Sadrita404/Twin-Key/Images/48.png

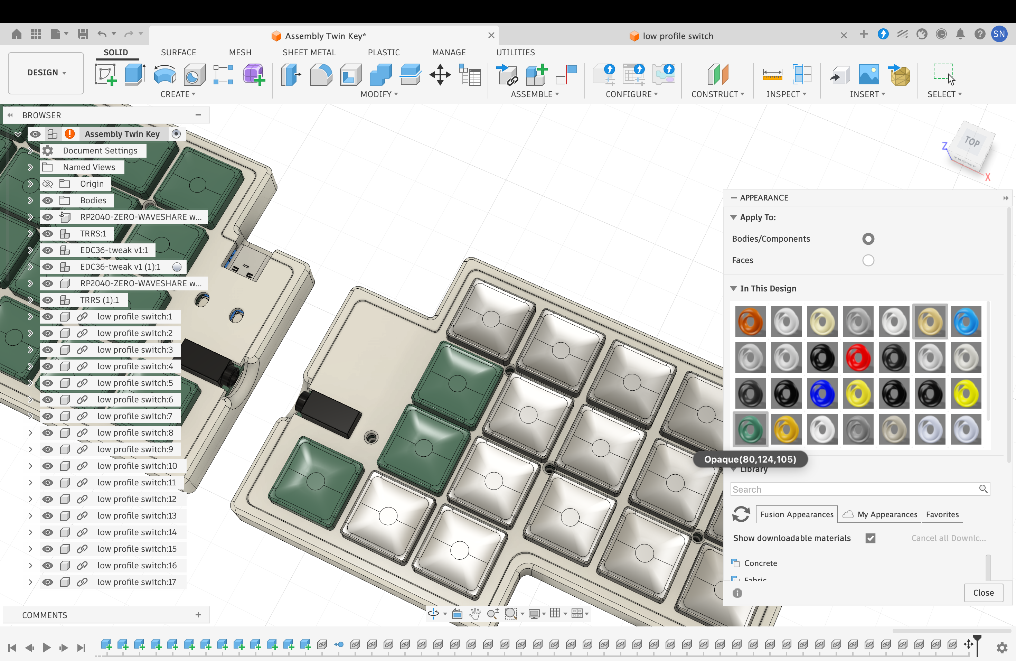
Images/48.png
