Sadrita404/Twin-Key/Bill/bill 1.png

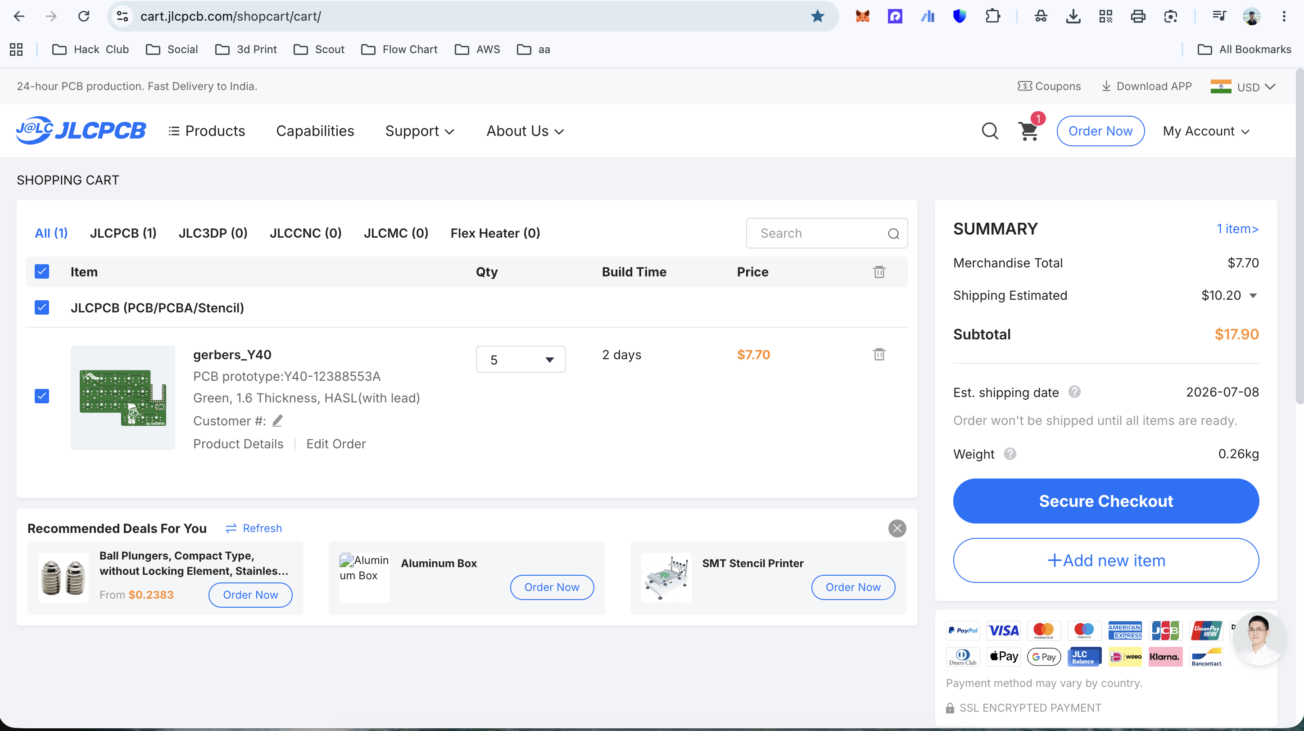
Bill/bill 1.png
