Sadrita404/Twin-Key/Bill/bill 2.png

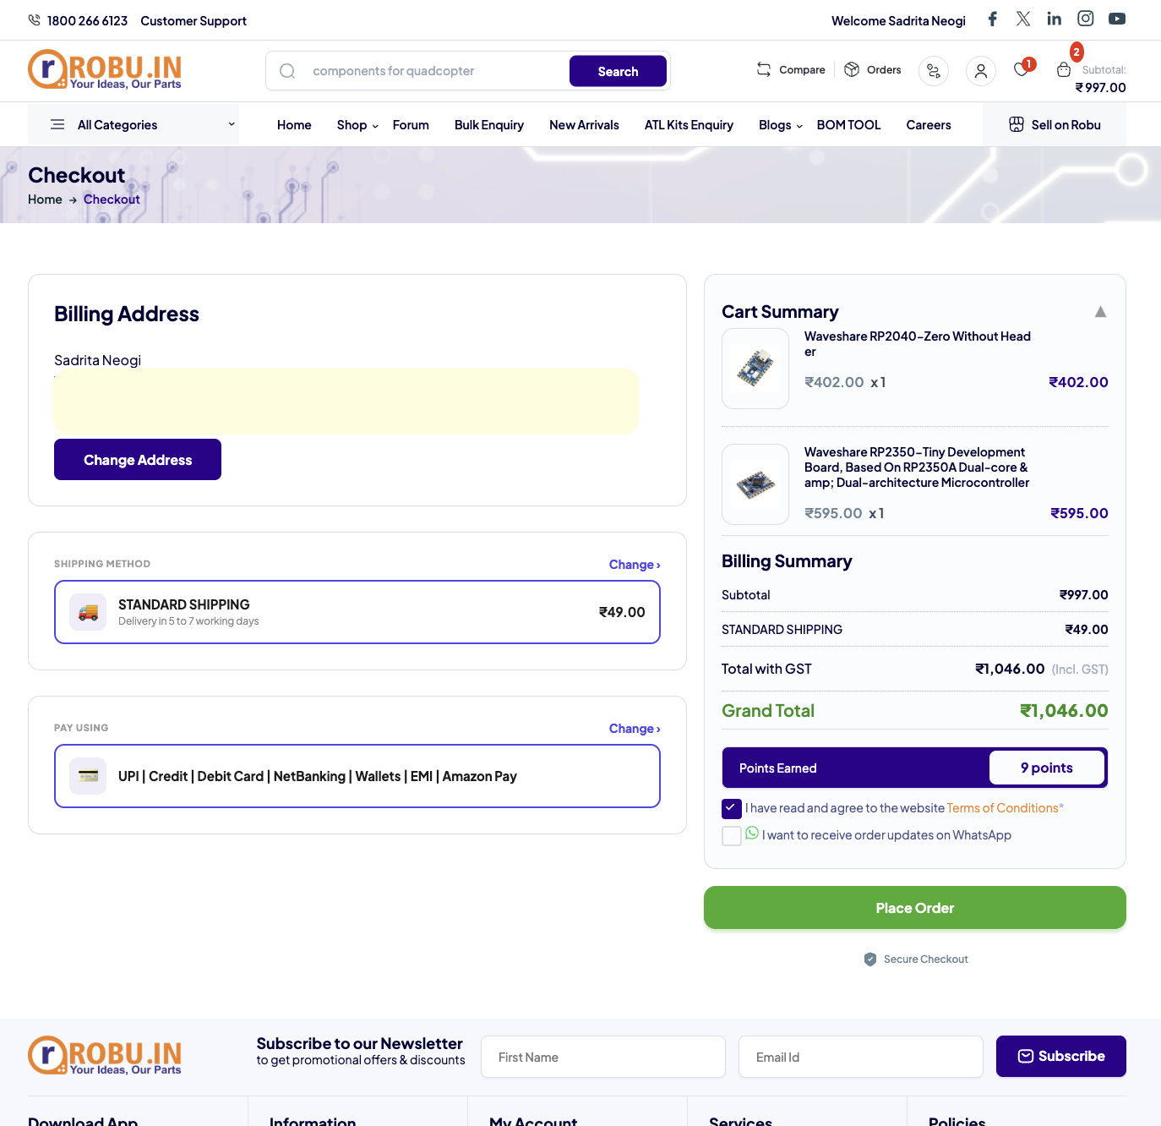
Bill/bill 2.png
