Sadrita404/Twin-Key/Bill/bill 3.png

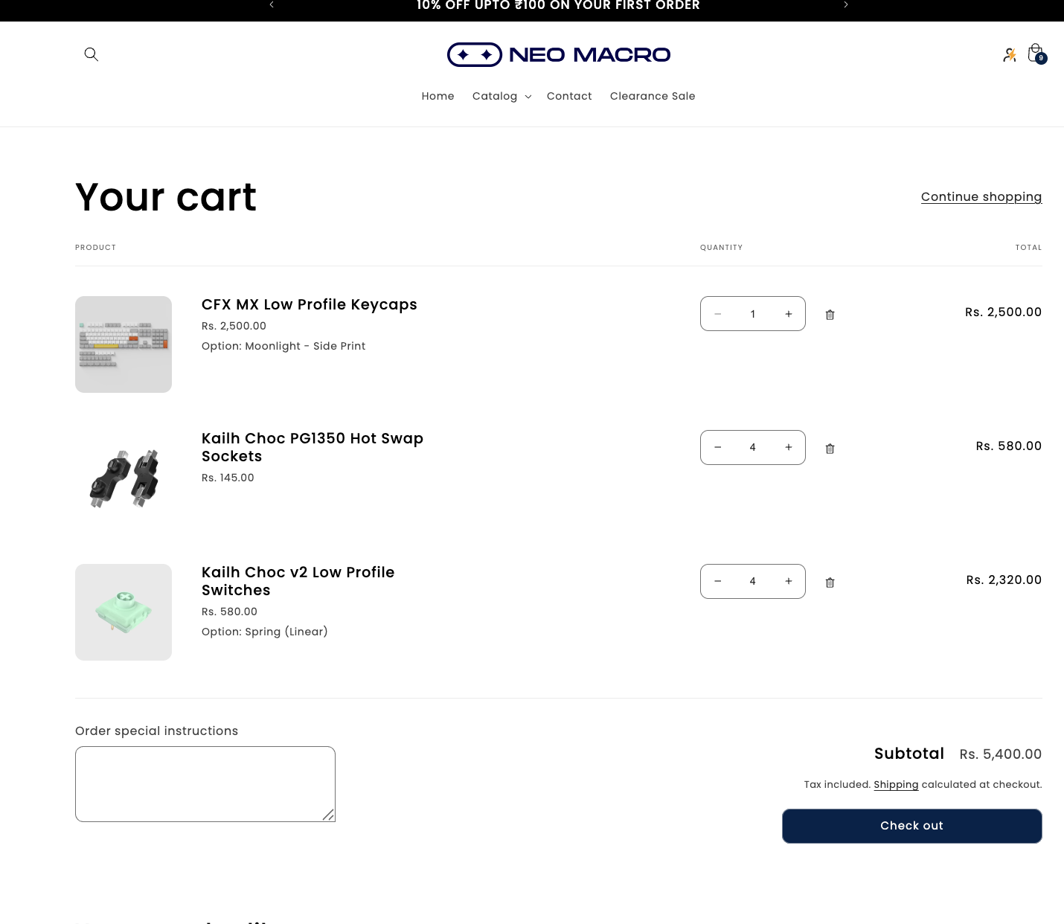
Bill/bill 3.png
