Sadrita404/Twin-Key/Bill/bill 4.png

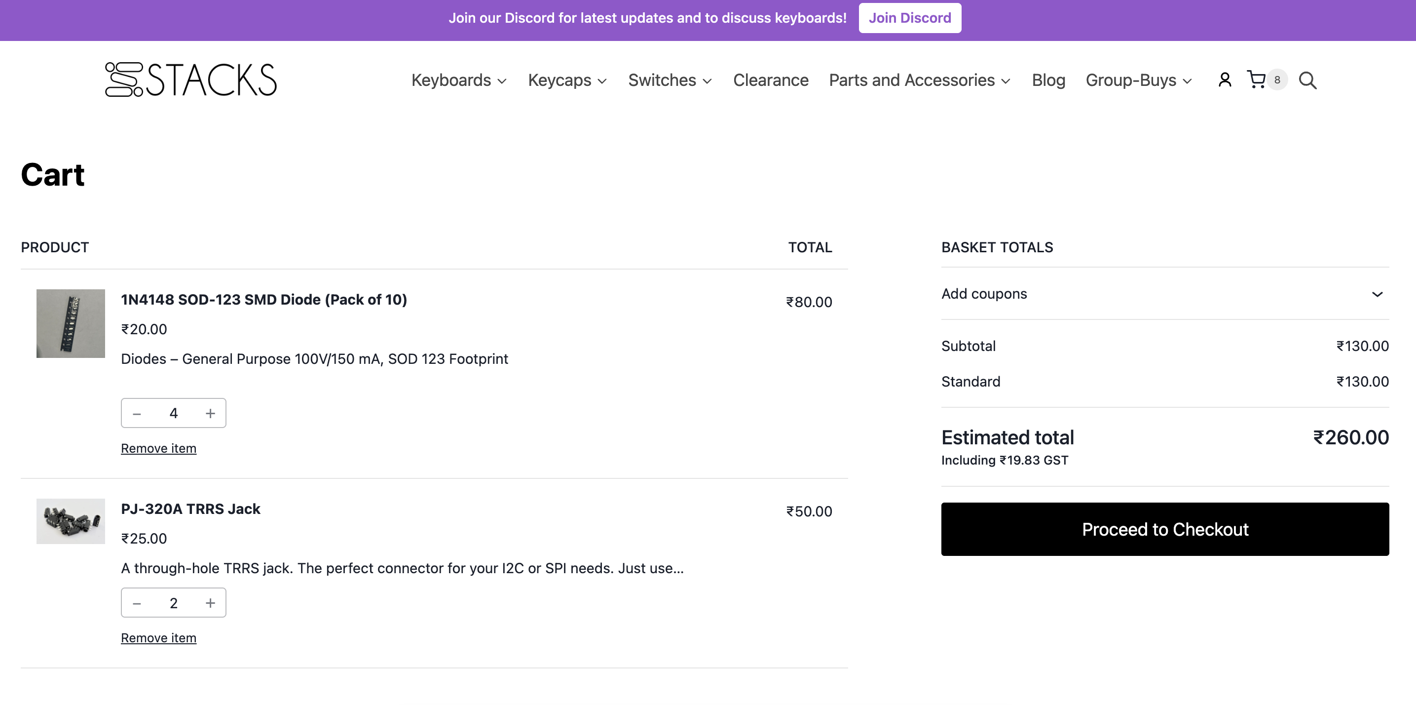
Bill/bill 4.png
