Sadrita404/Twin-Key/Bill/bill 5.png

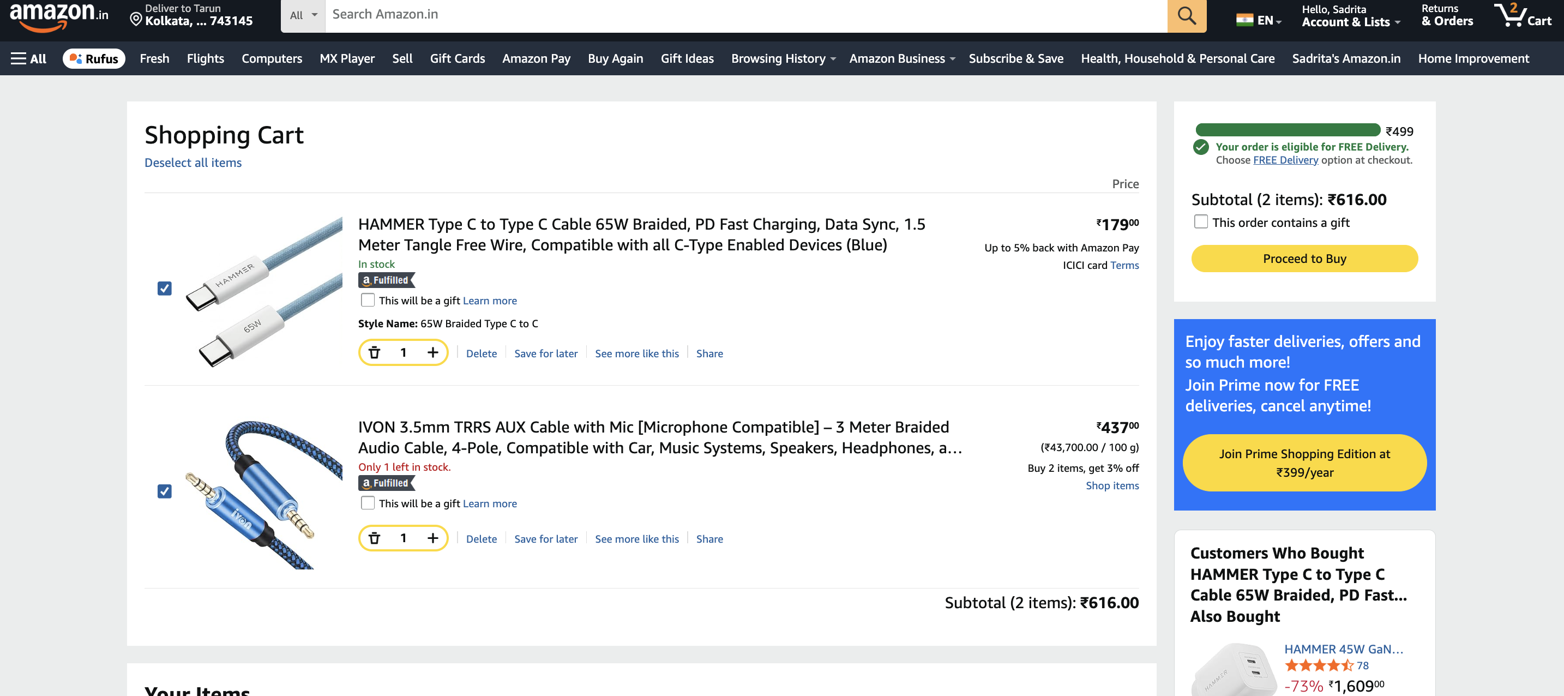
Bill/bill 5.png
