Sadrita404/Twin-Key/Images/1.png

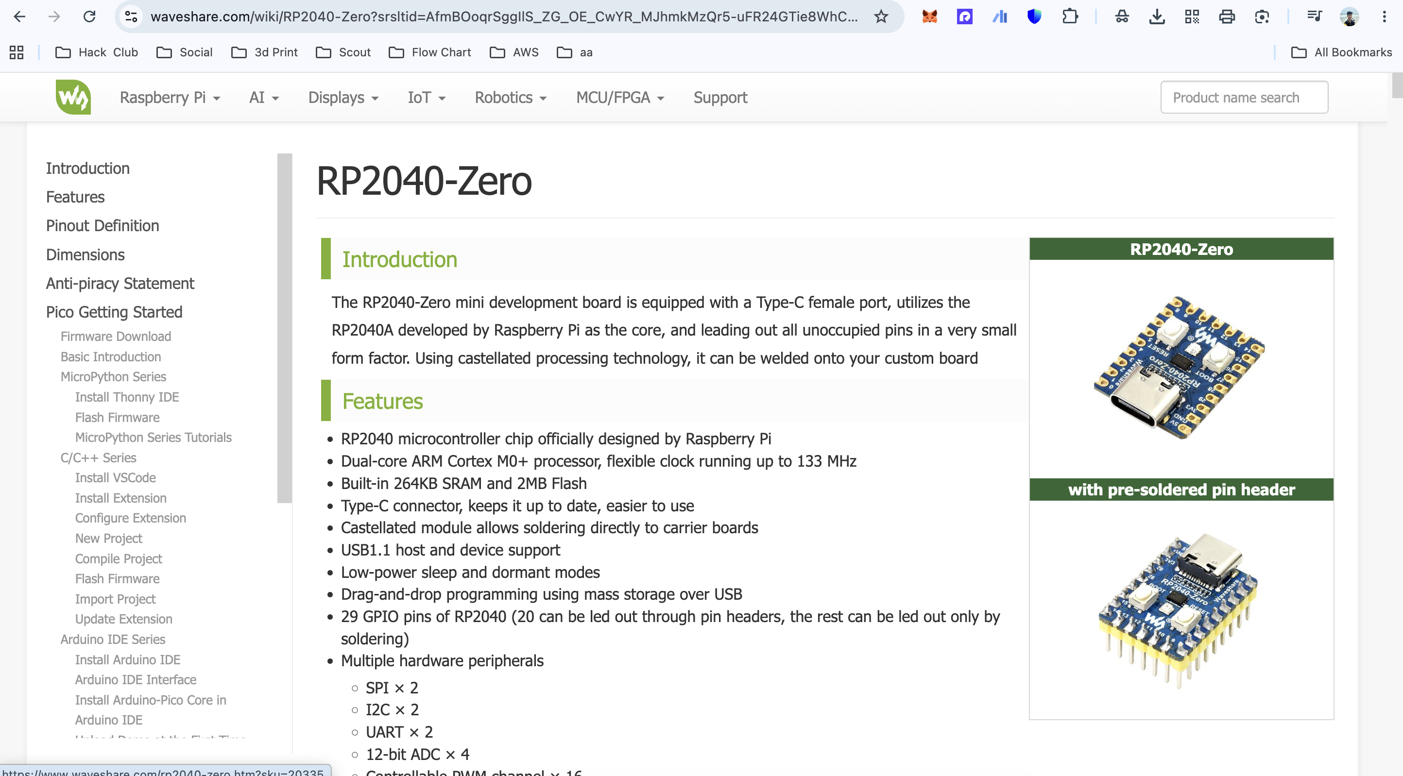
Images/1.png
