Sadrita404/Twin-Key/Images/2.png

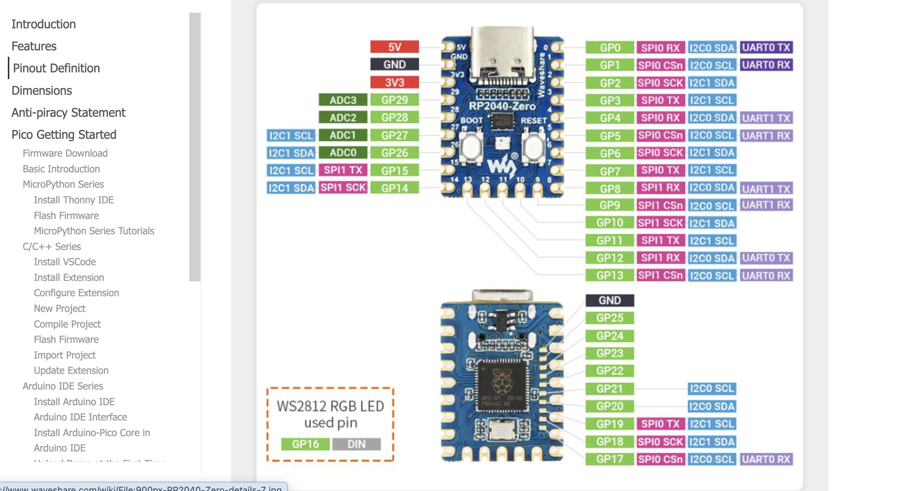
Images/2.png
