Sadrita404/Twin-Key/Images/3.png

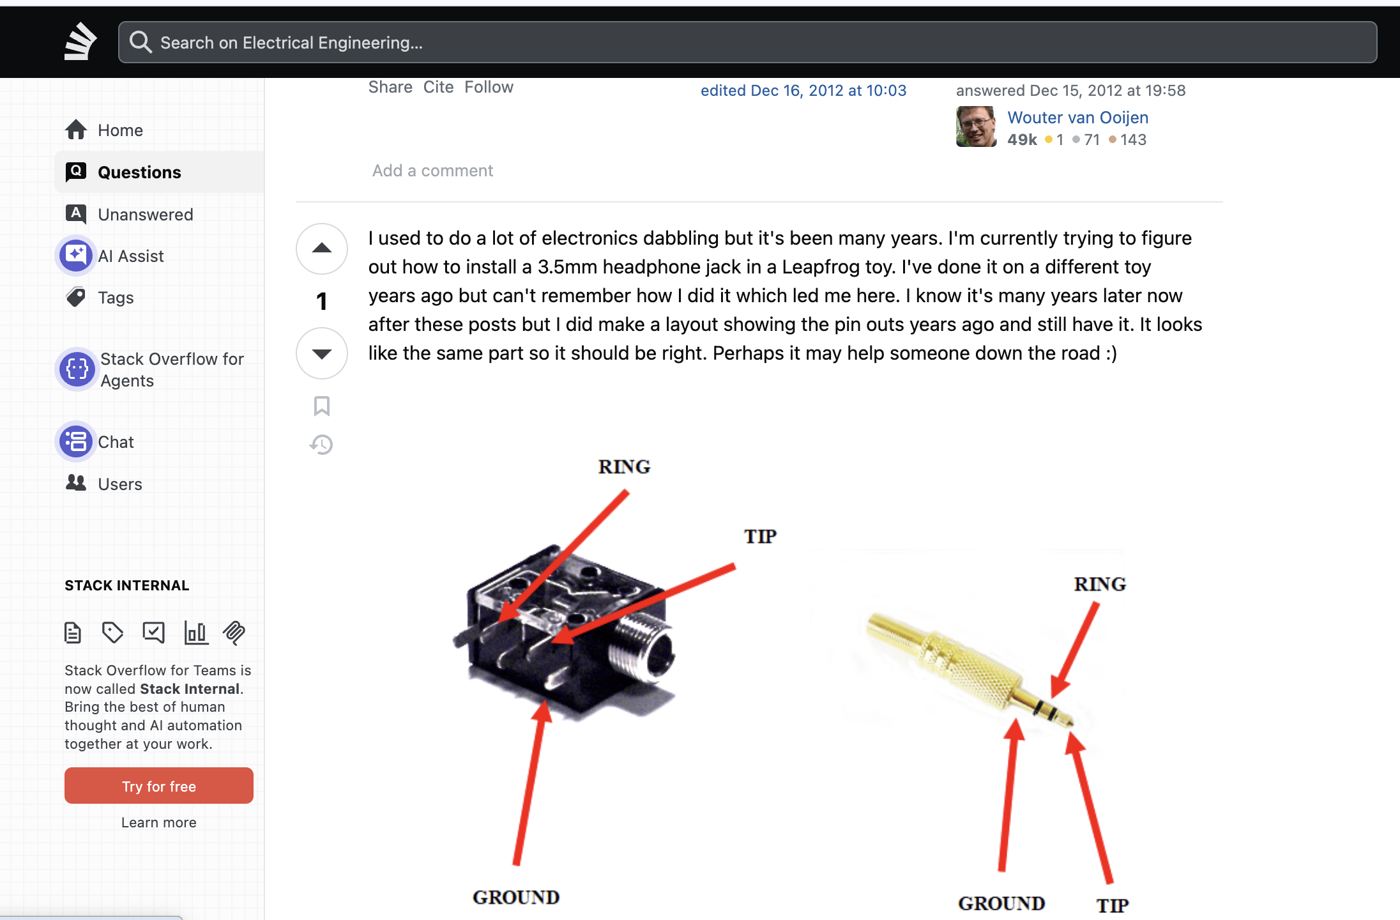
Images/3.png
