Sadrita404/Twin-Key/Images/4.png

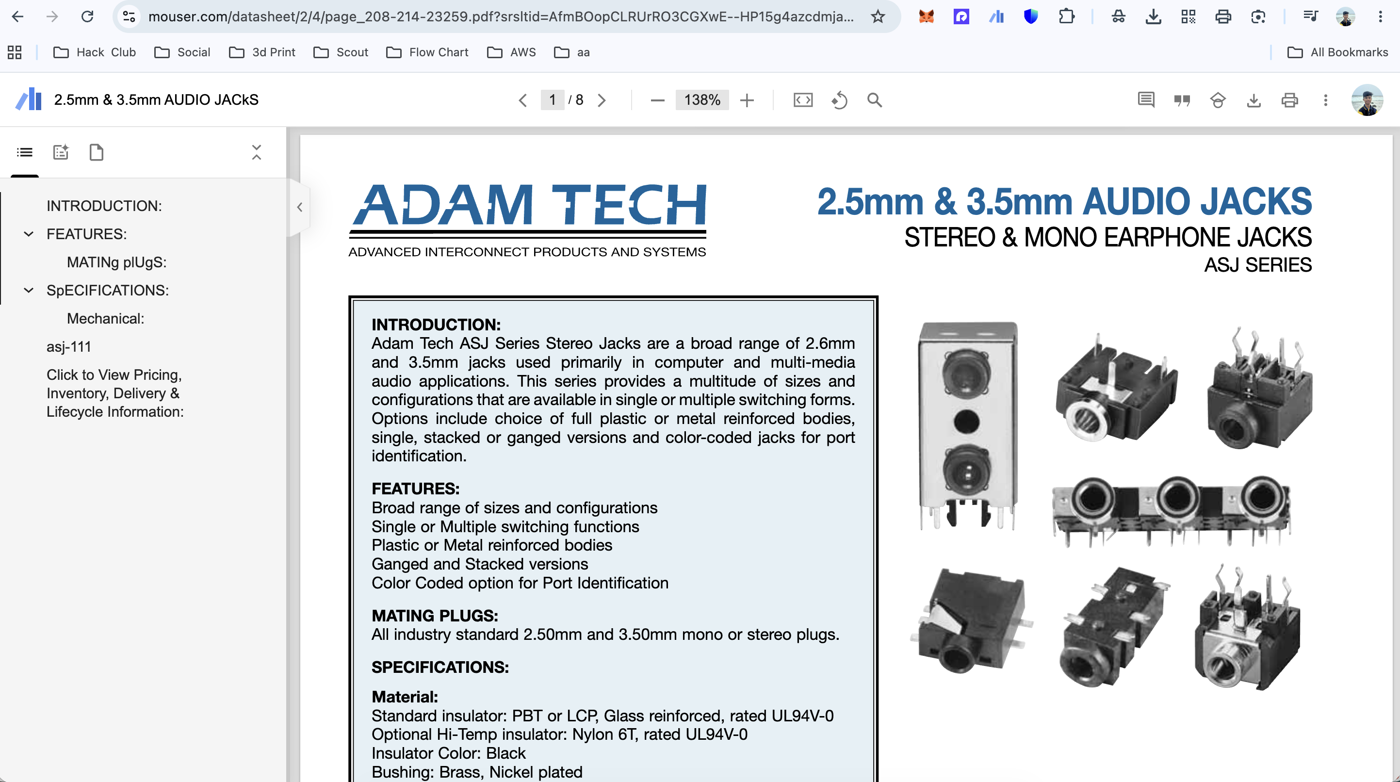
Images/4.png
