Sadrita404/Twin-Key/Images/5.png

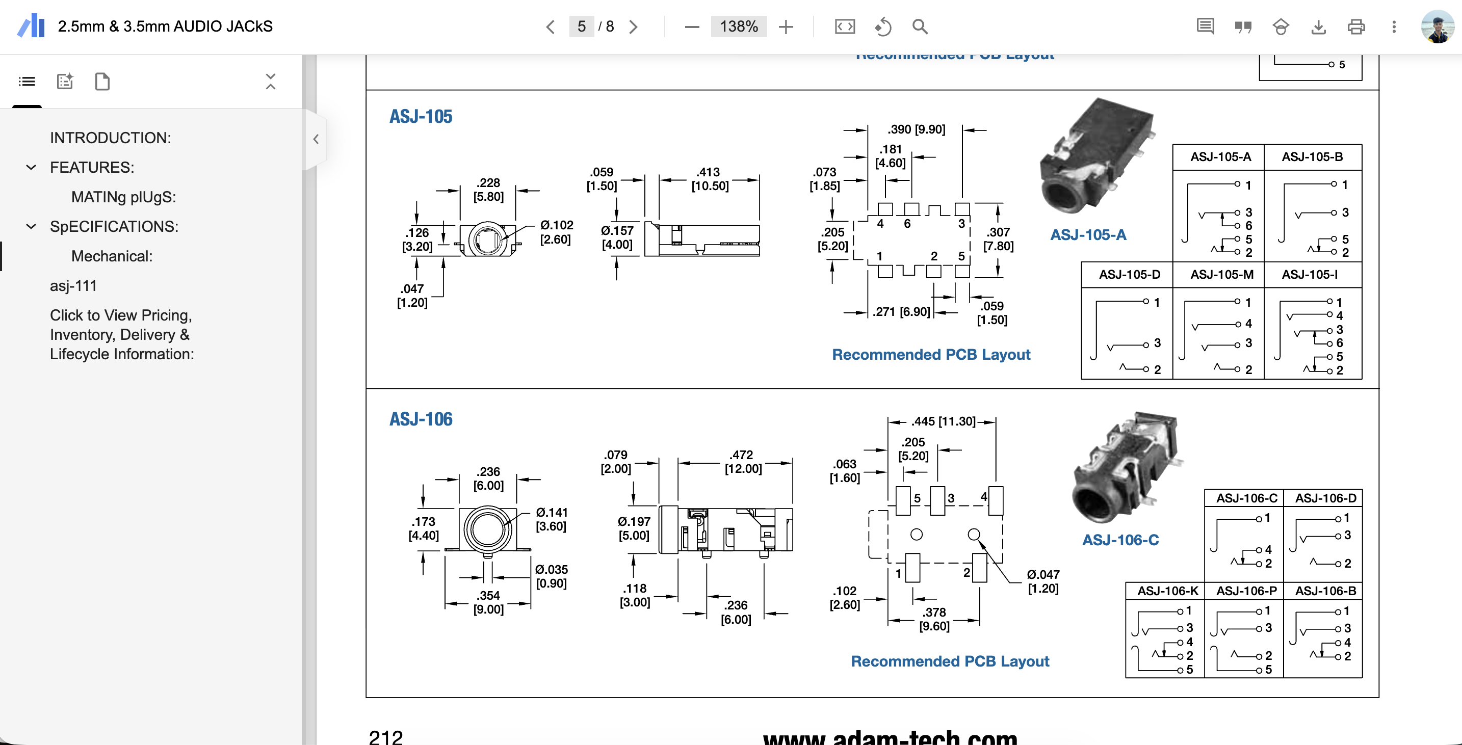
Images/5.png
