Sadrita404/Twin-Key/Images/6.png

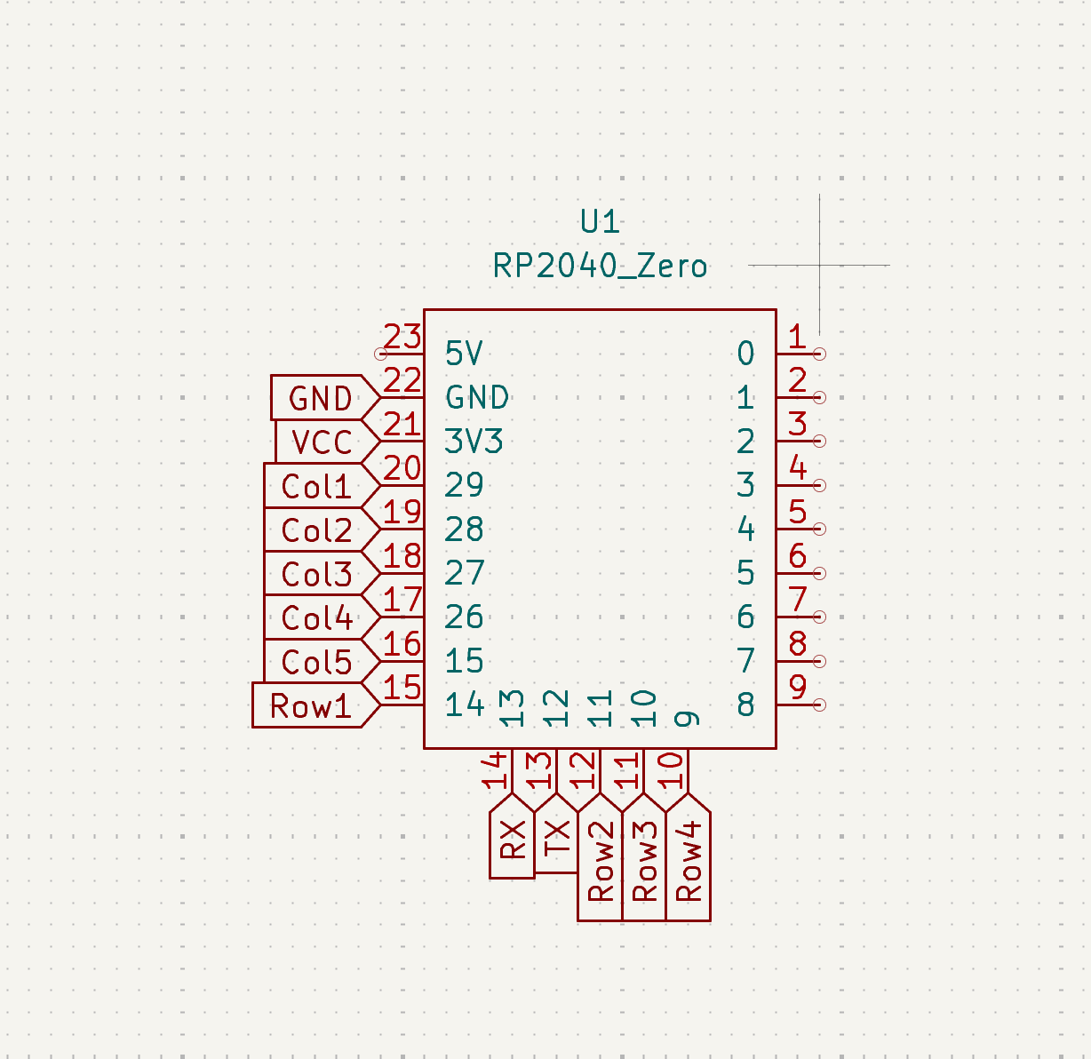
Images/6.png
