Sadrita404/Twin-Key/Images/7.png

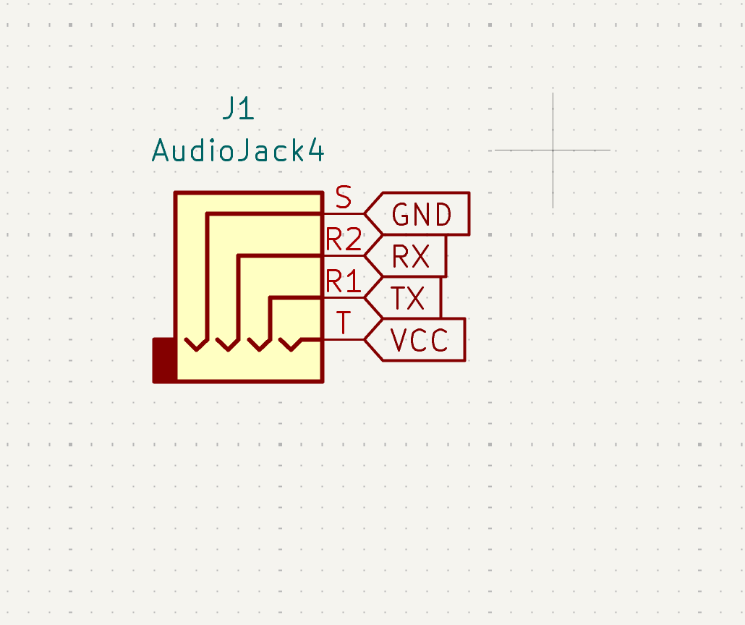
Images/7.png
