Sadrita404/Twin-Key/Images/8.png

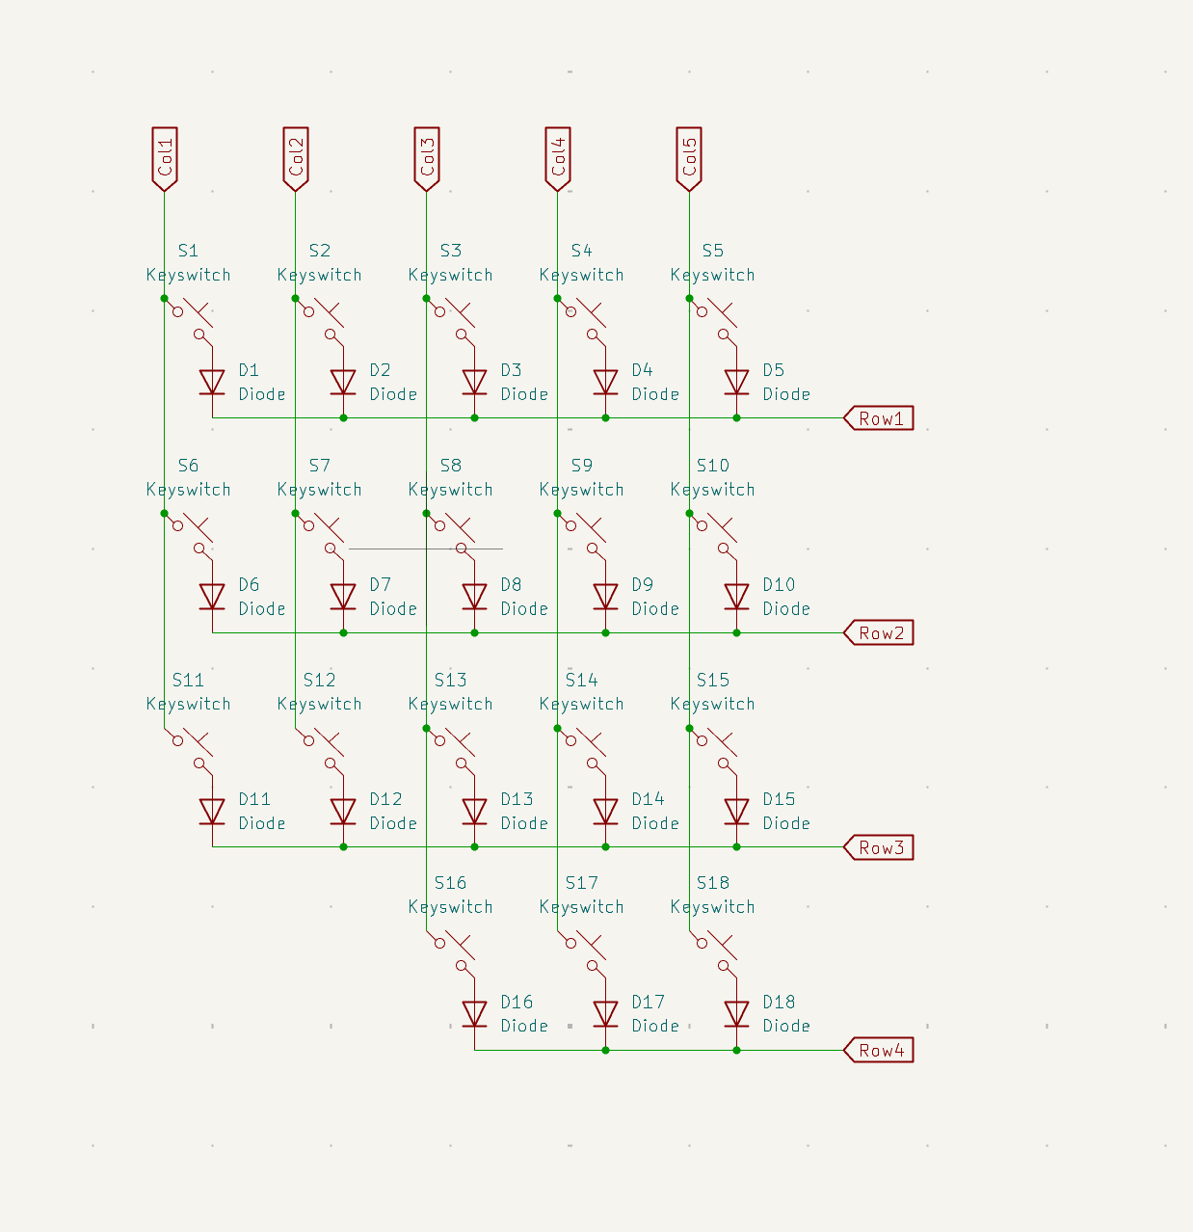
Images/8.png
