Sadrita404/Twin-Key/Images/9.png

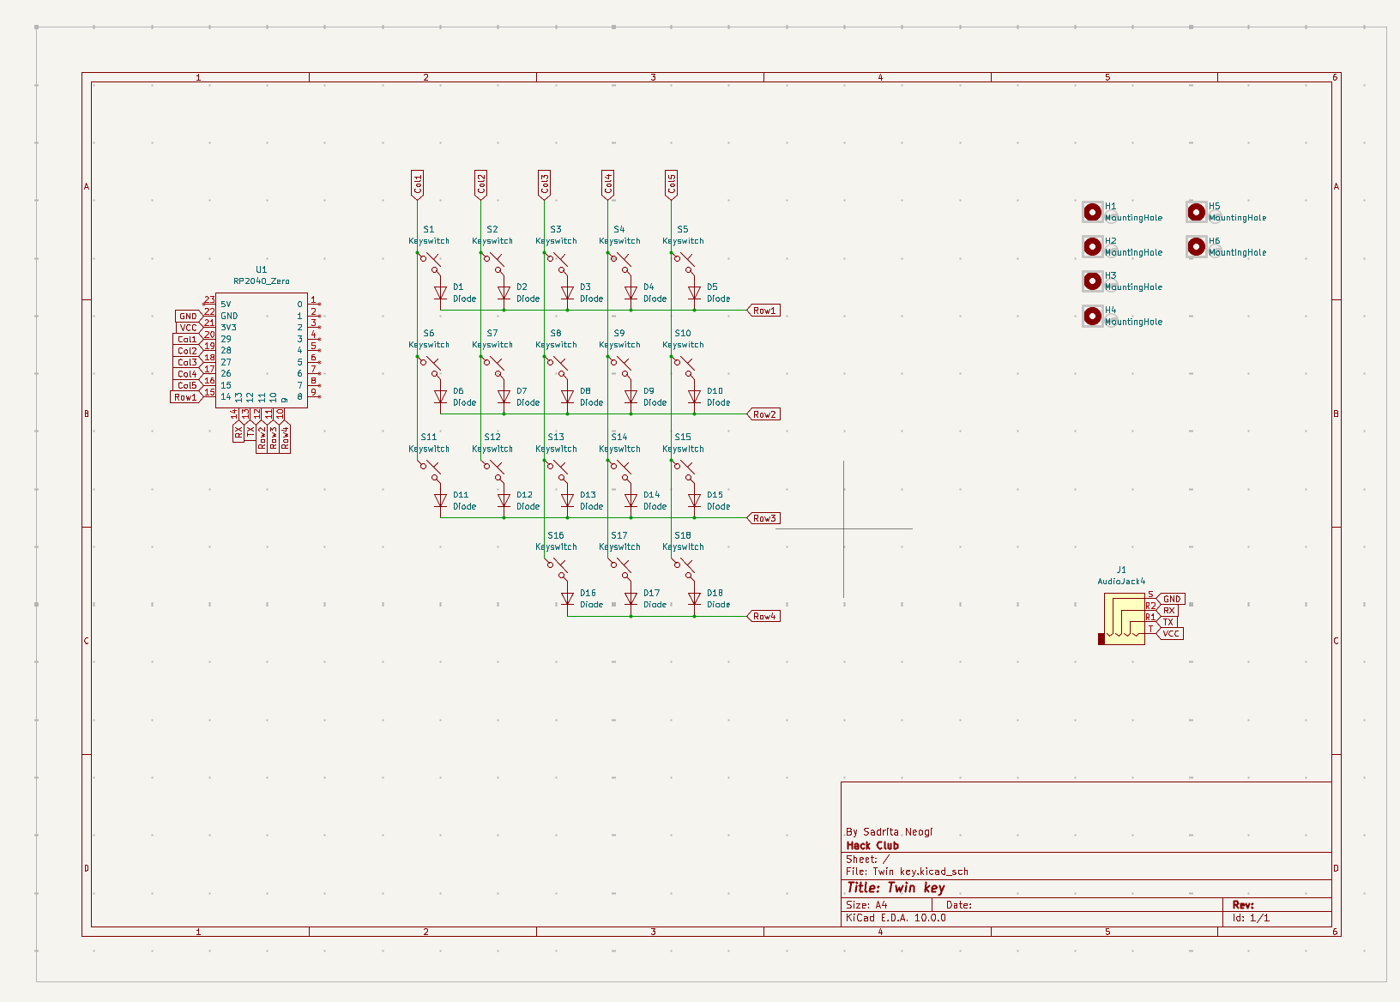
Images/9.png
