Sadrita404/Twin-Key/Images/10.png

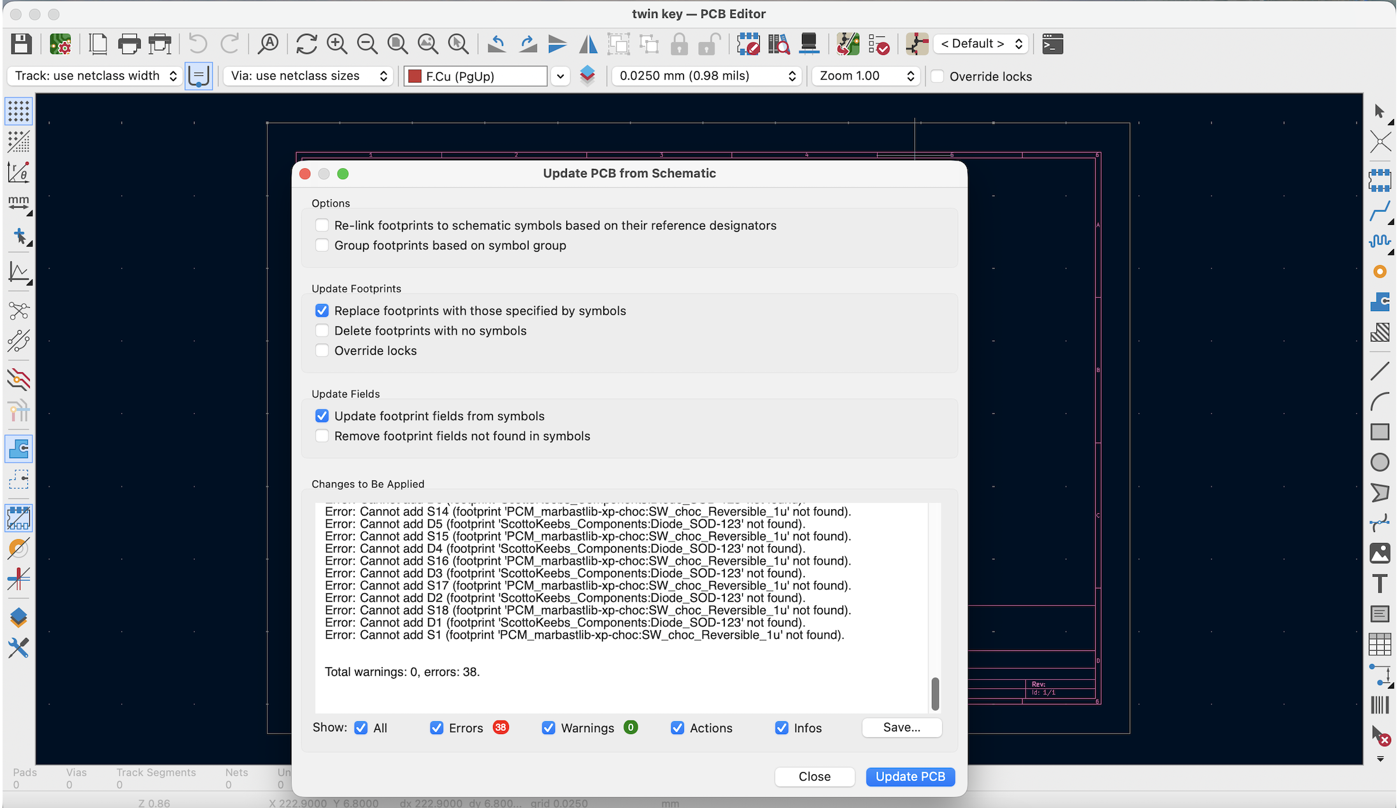
Images/10.png
