Sadrita404/Twin-Key/Images/11.png

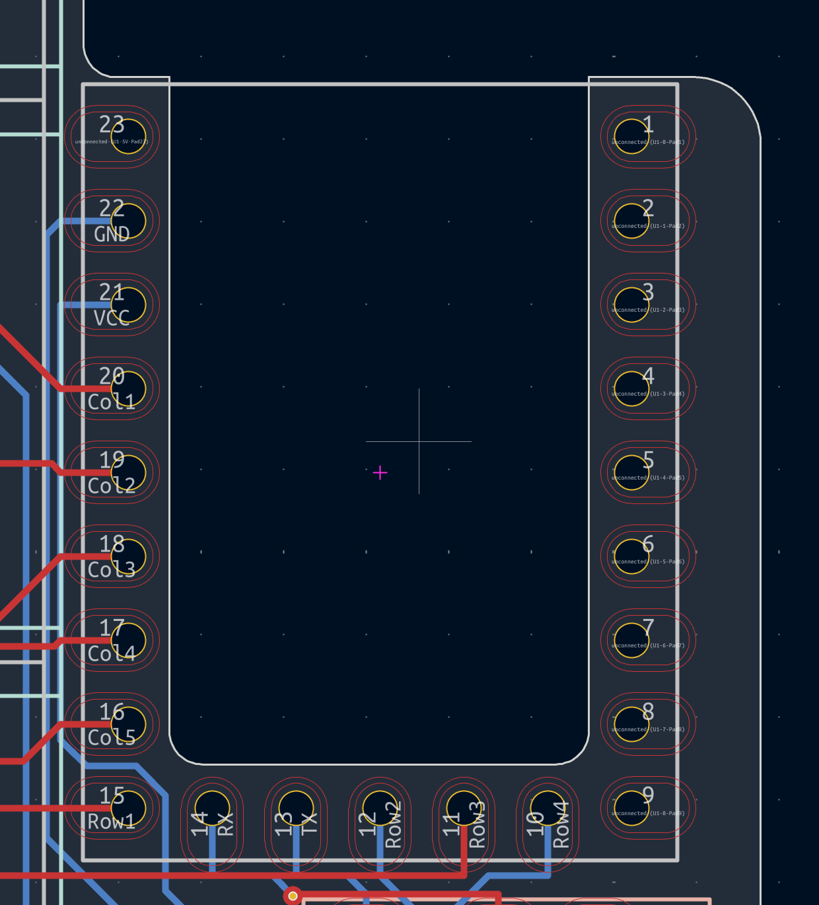
Images/11.png
