Sadrita404/Twin-Key/Images/12.png

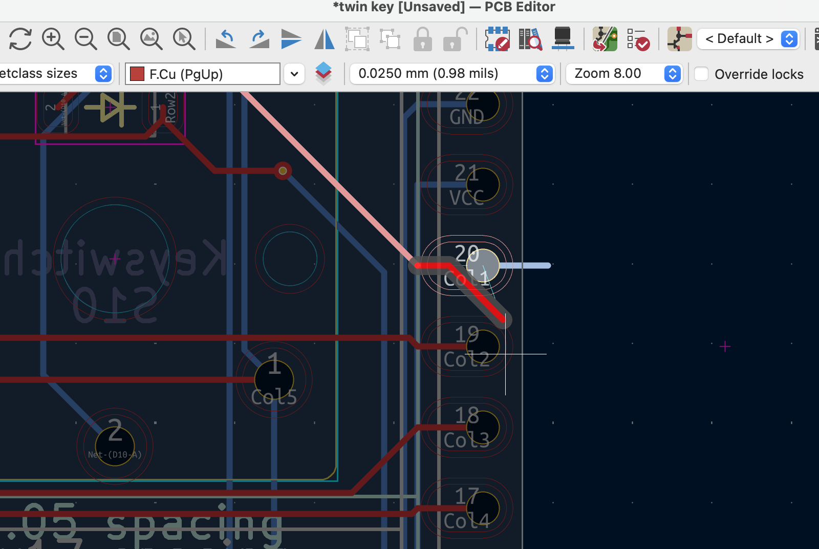
Images/12.png
