Sadrita404/Twin-Key/Images/13.png

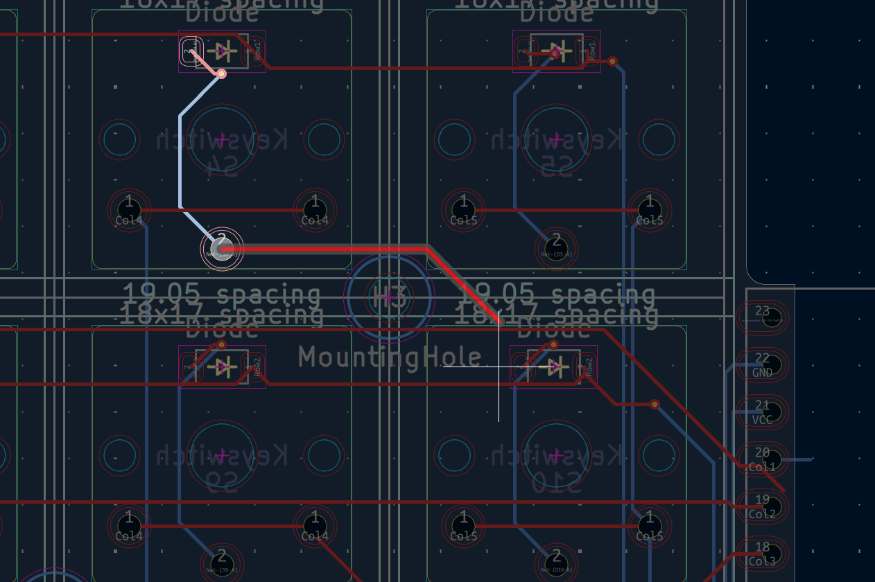
Images/13.png
