Sadrita404/Twin-Key/Images/14.png

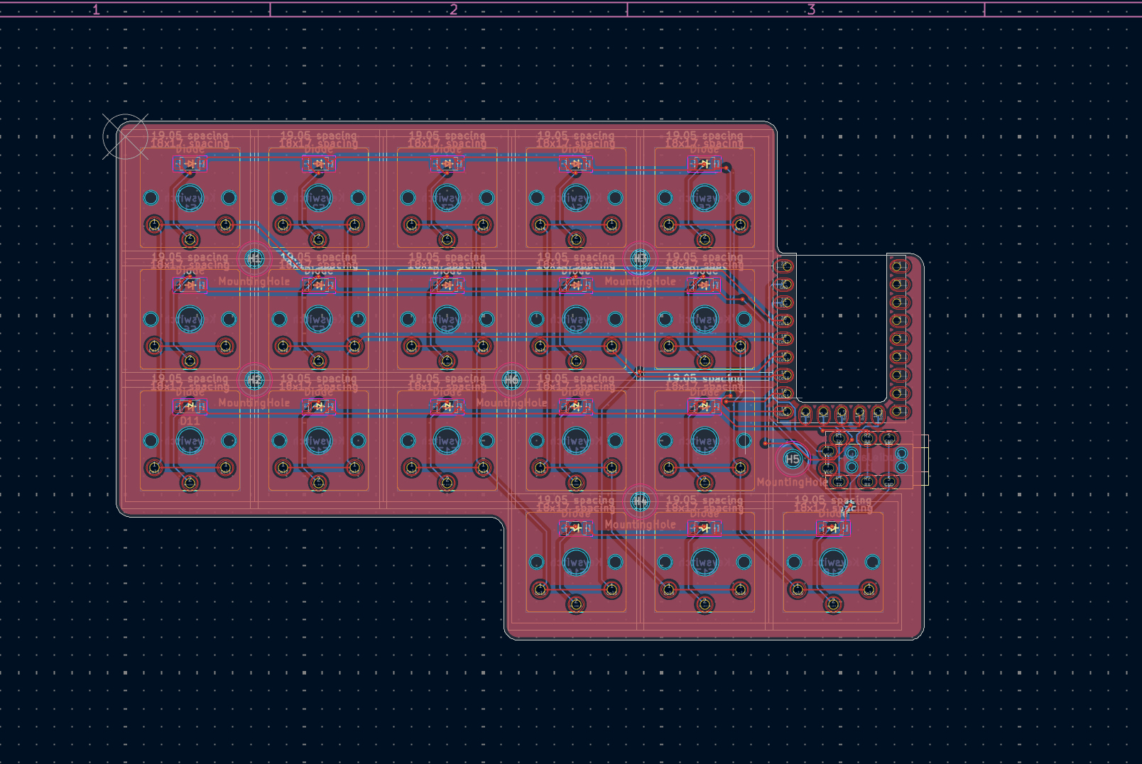
Images/14.png
