Sadrita404/Twin-Key/Images/15.png

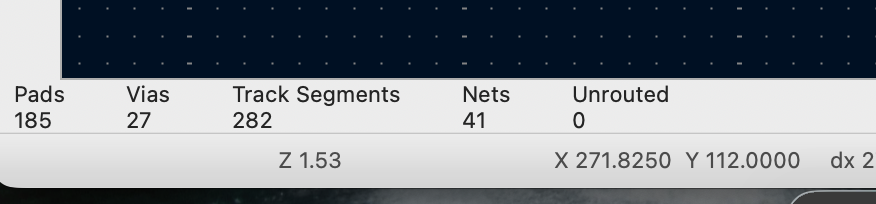
Images/15.png
