Sadrita404/Twin-Key/Images/16.png

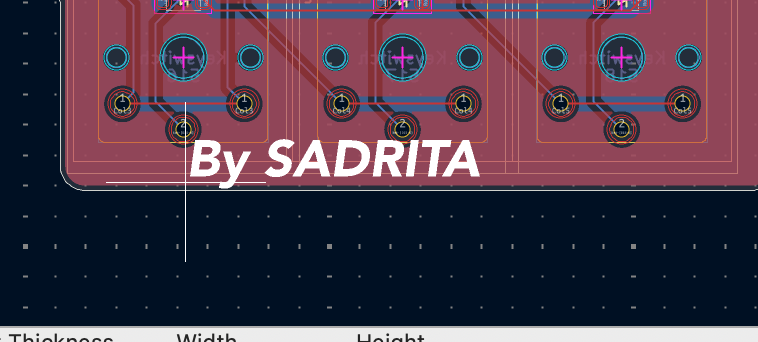
Images/16.png
