Sadrita404/Twin-Key/Images/17.png

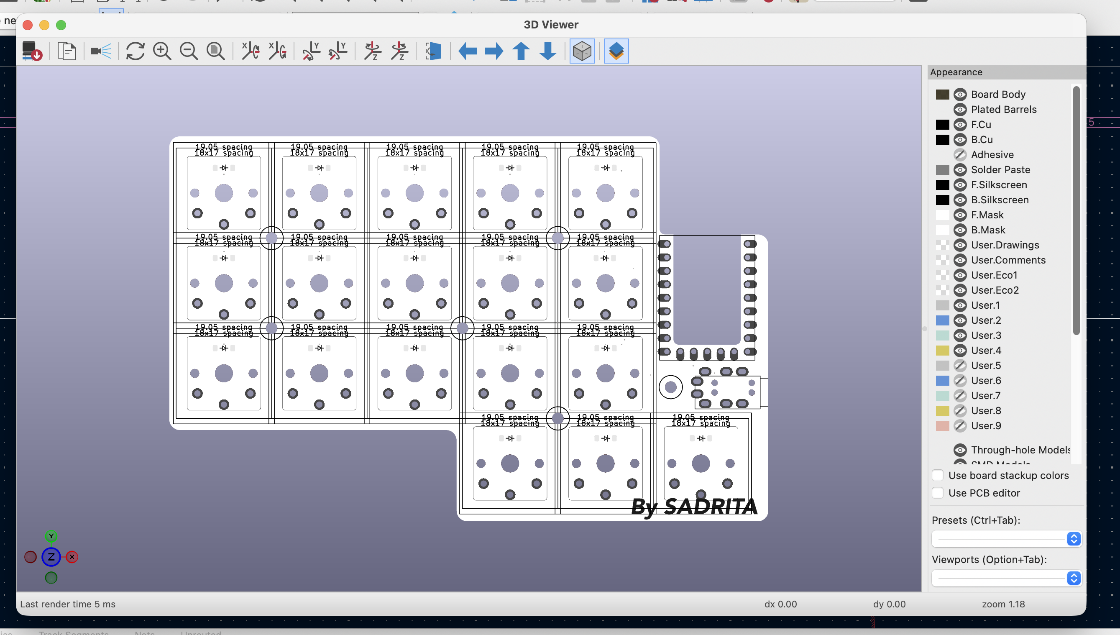
Images/17.png
