Sadrita404/Twin-Key/Images/19.png

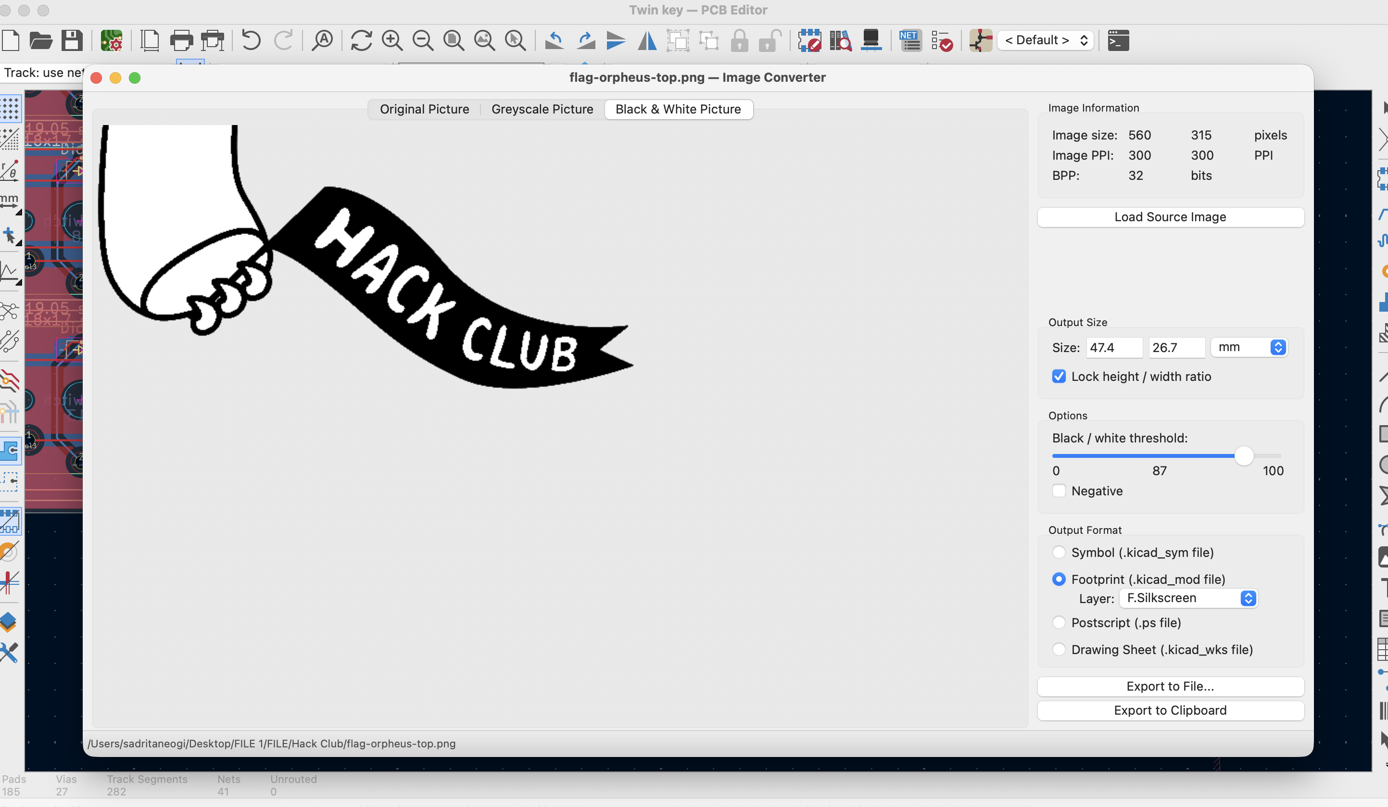
Images/19.png
