Sadrita404/Twin-Key/Images/20.png

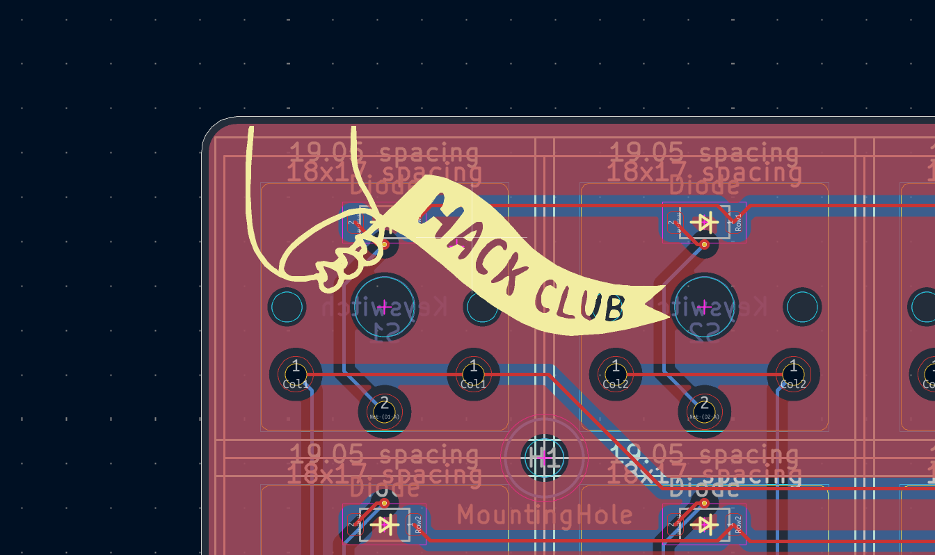
Images/20.png
