Sadrita404/Twin-Key/Images/21.png

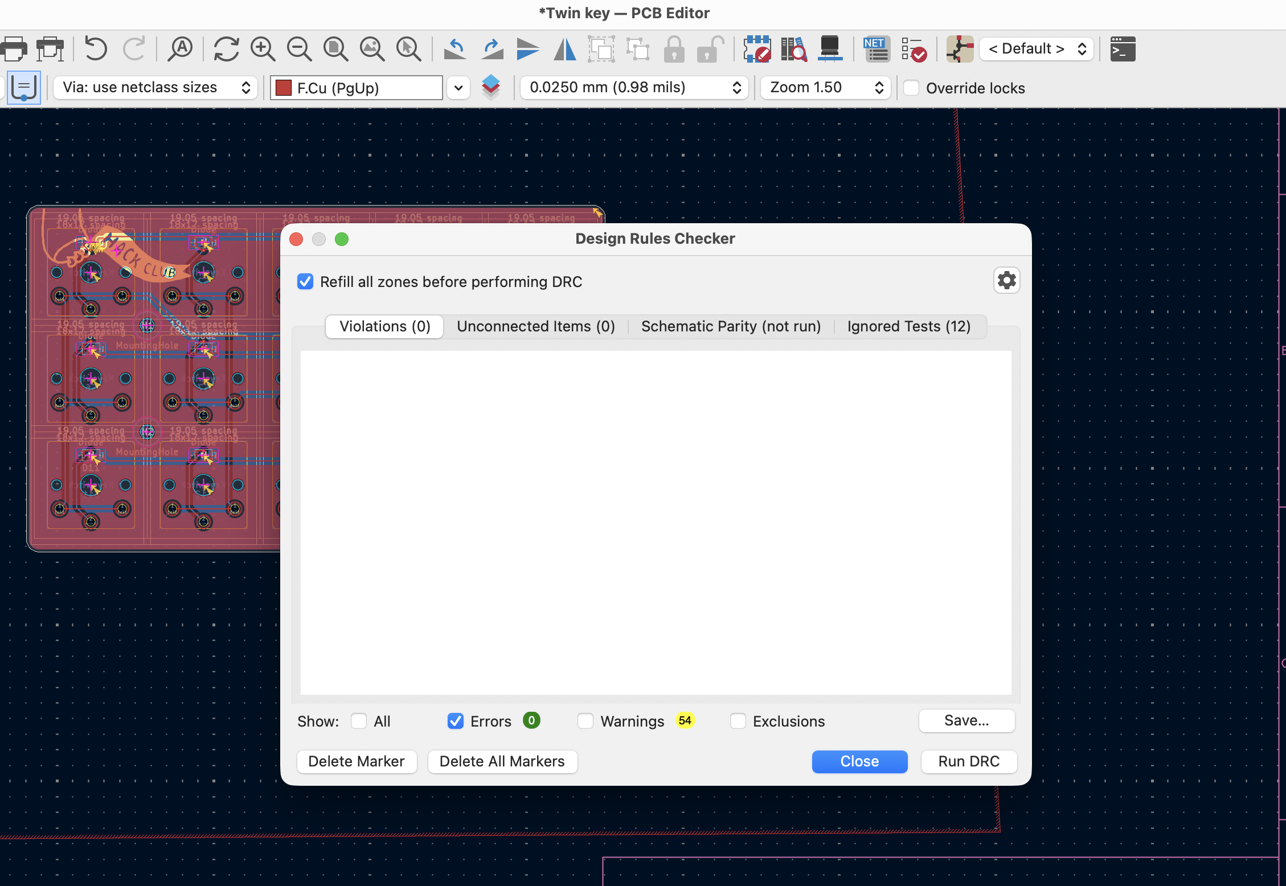
Images/21.png
