Sadrita404/Twin-Key/Images/22.png

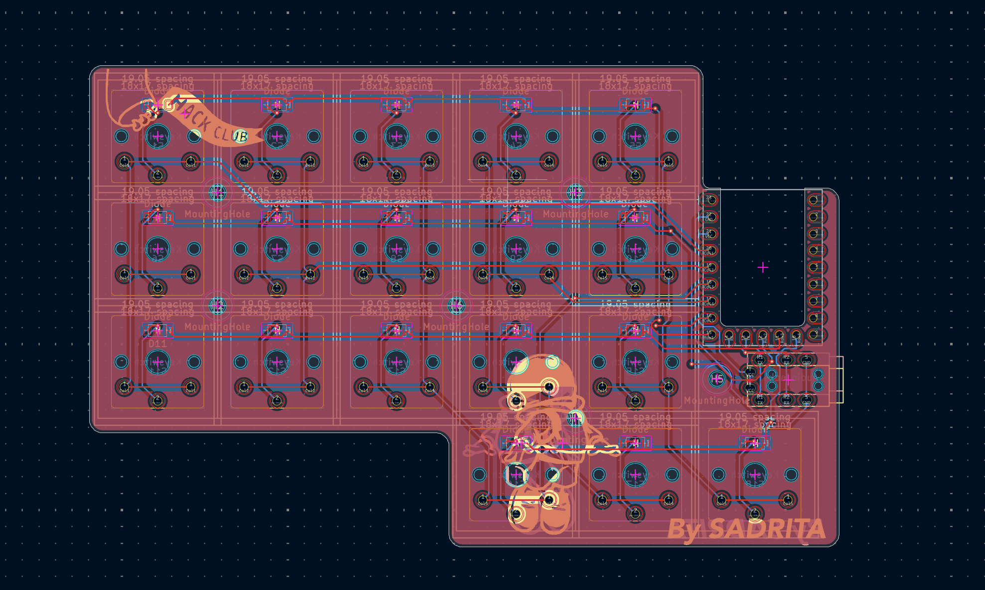
Images/22.png
