Sadrita404/Twin-Key/Images/23.png

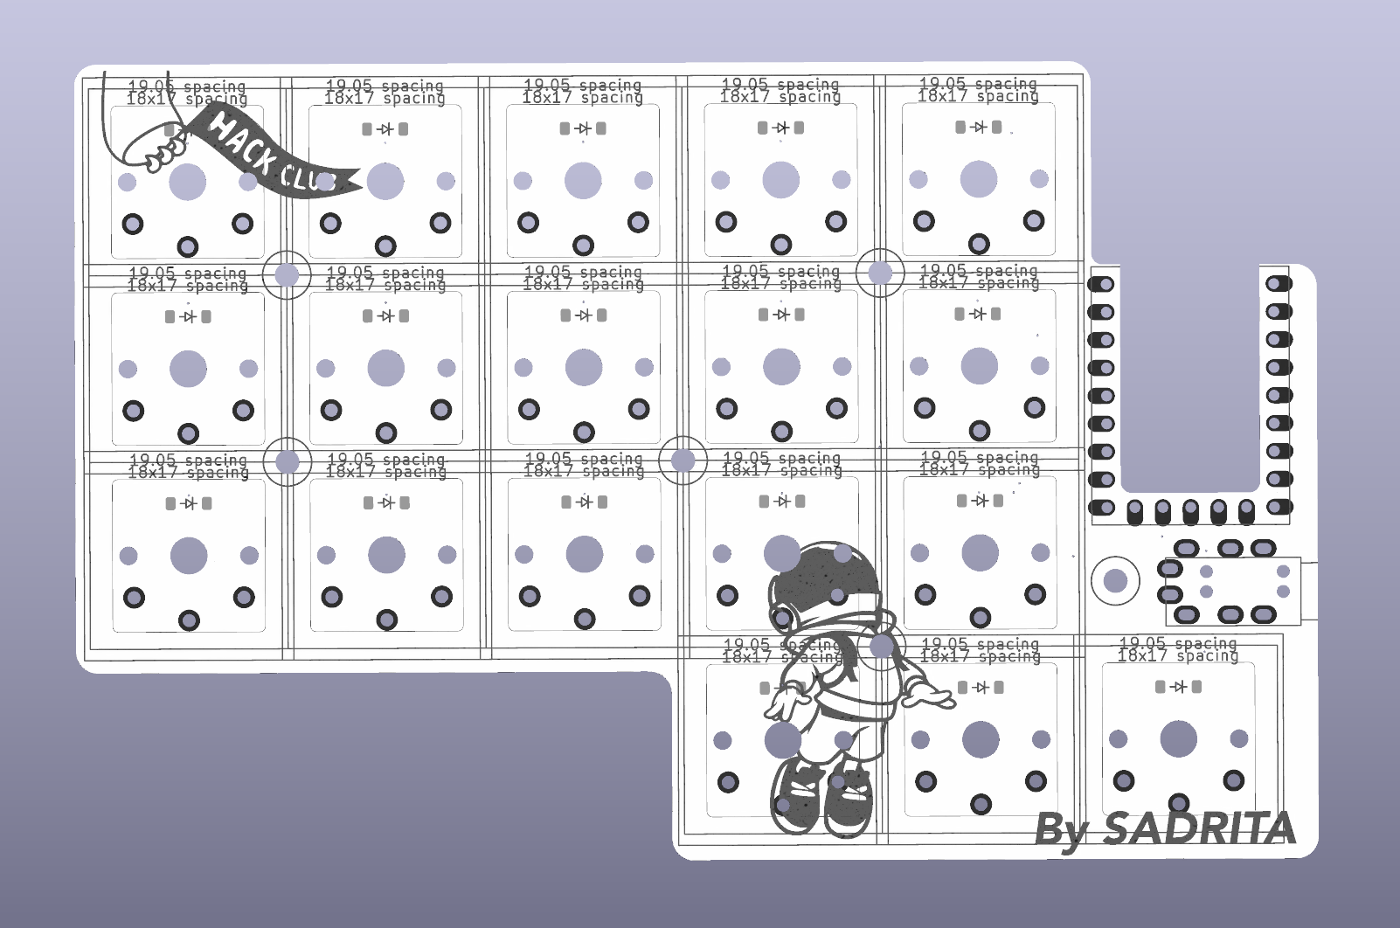
Images/23.png
