Sadrita404/Twin-Key/Images/24.png

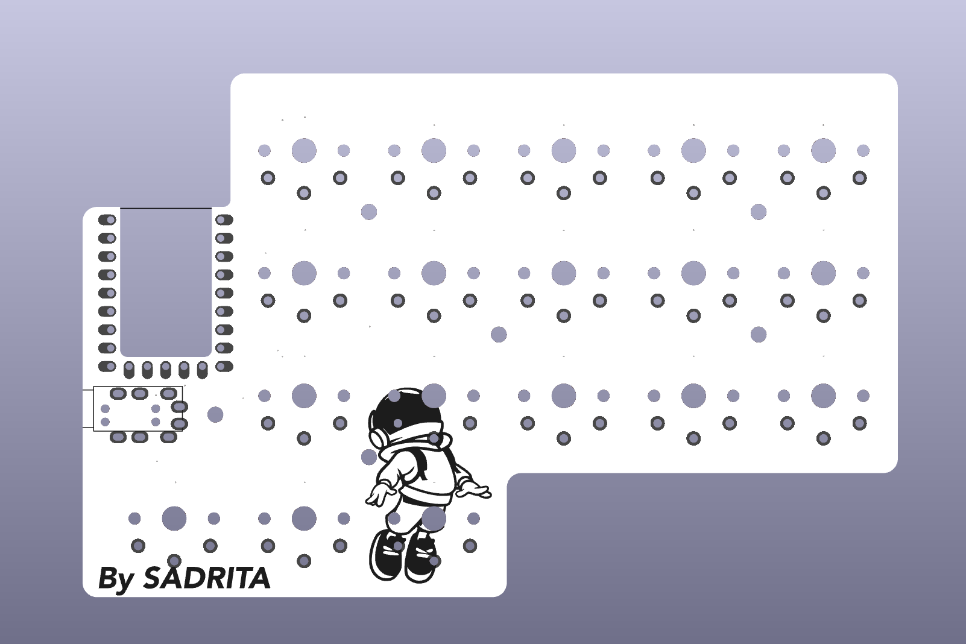
Images/24.png
