Sadrita404/Twin-Key/Images/25.png

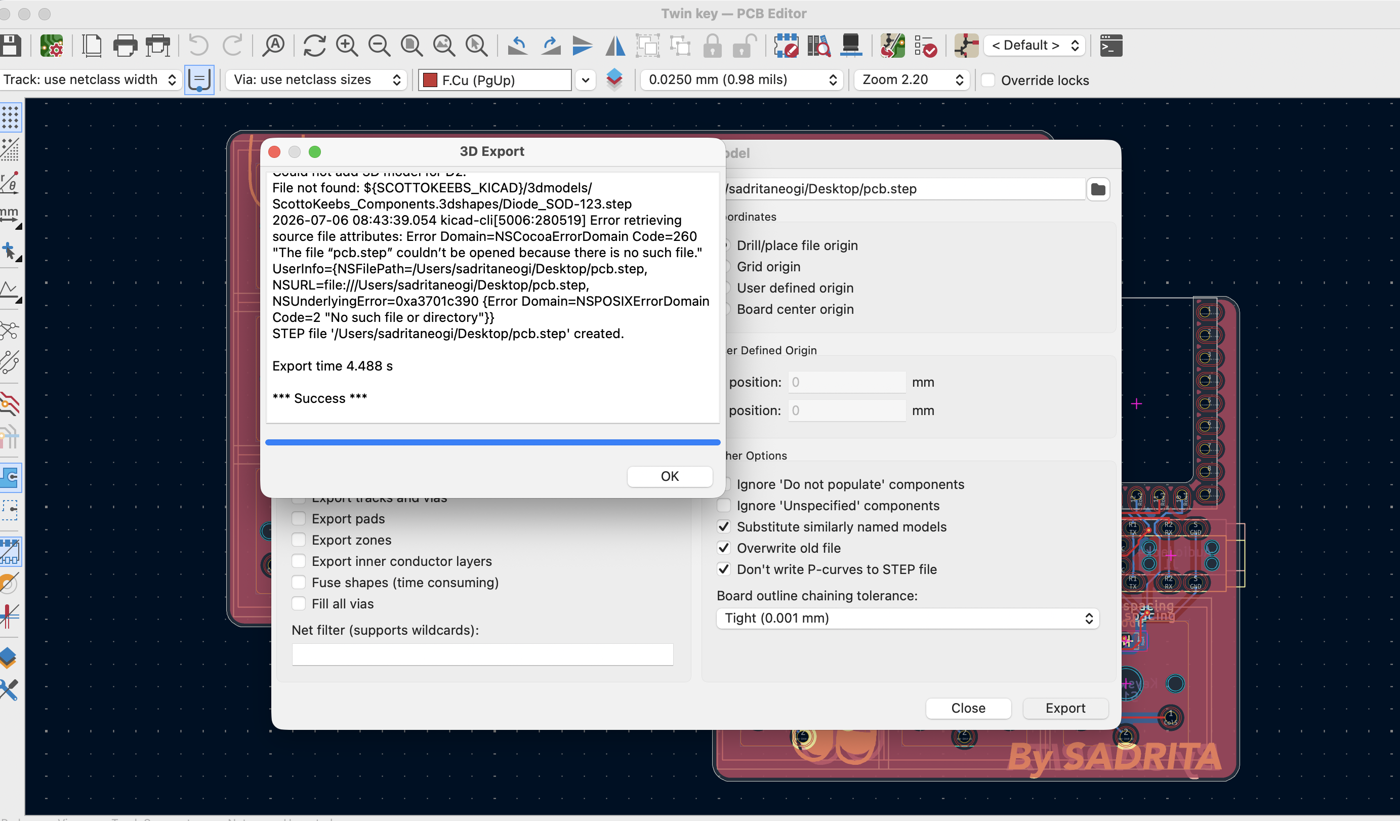
Images/25.png
