Sadrita404/Twin-Key/Images/26.png

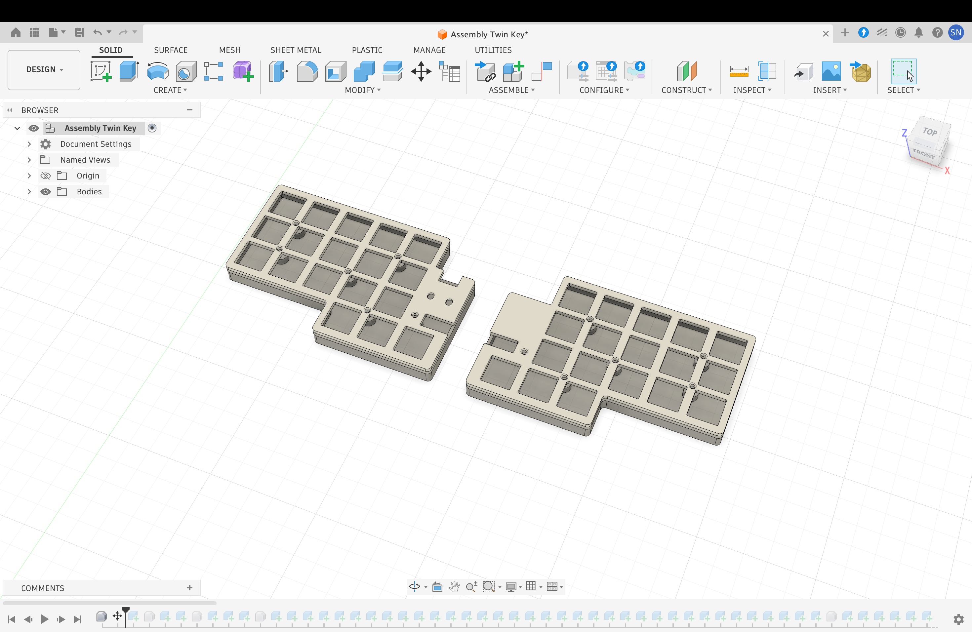
Images/26.png
