Sadrita404/Twin-Key/Images/27.png

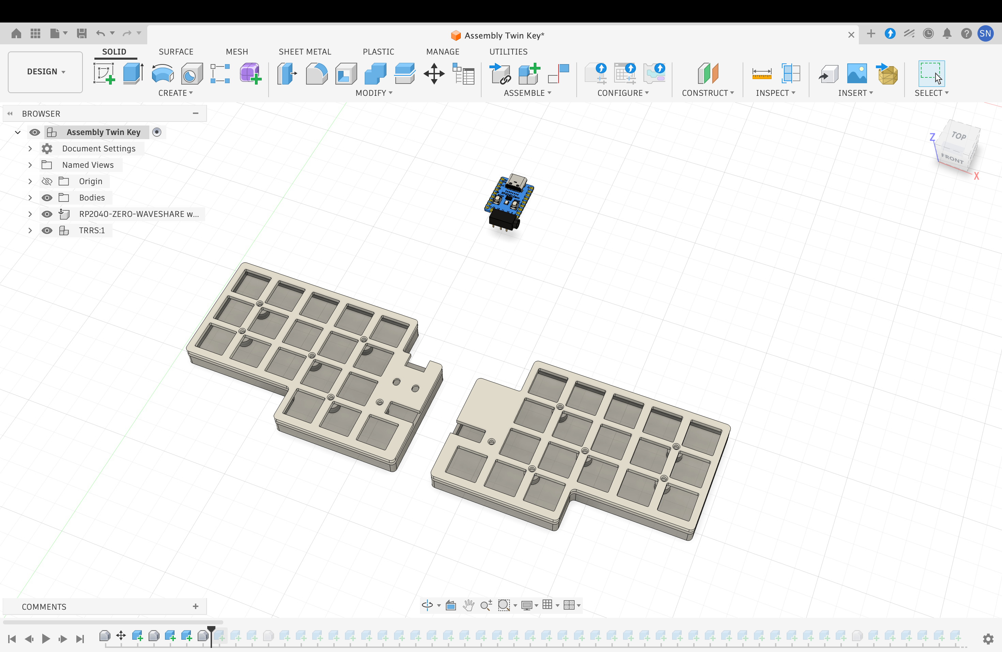
Images/27.png
