Sadrita404/Twin-Key/Images/28.png

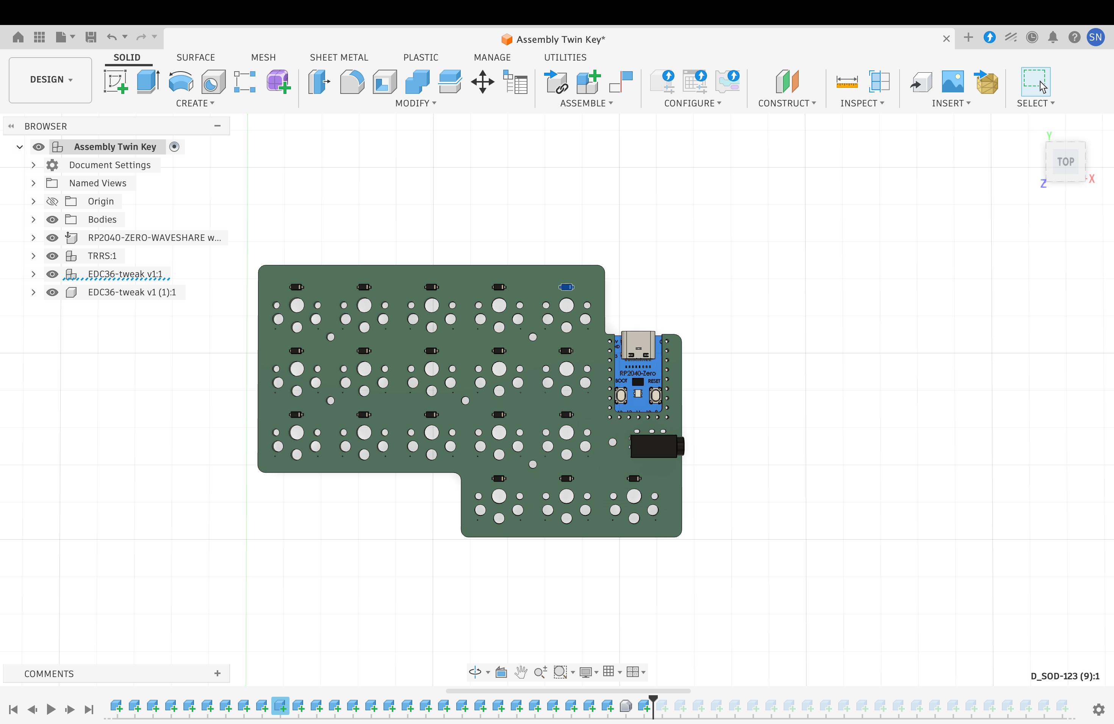
Images/28.png
