Sadrita404/Twin-Key/Images/29.png

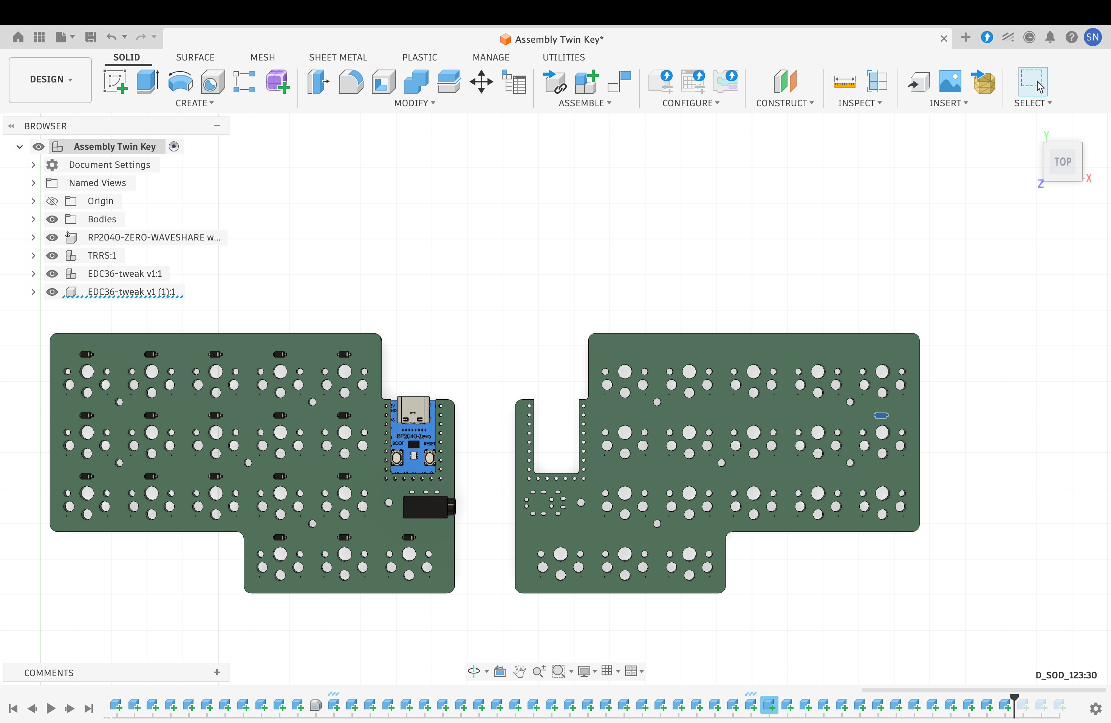
Images/29.png
