Sadrita404/Twin-Key/Images/30.png

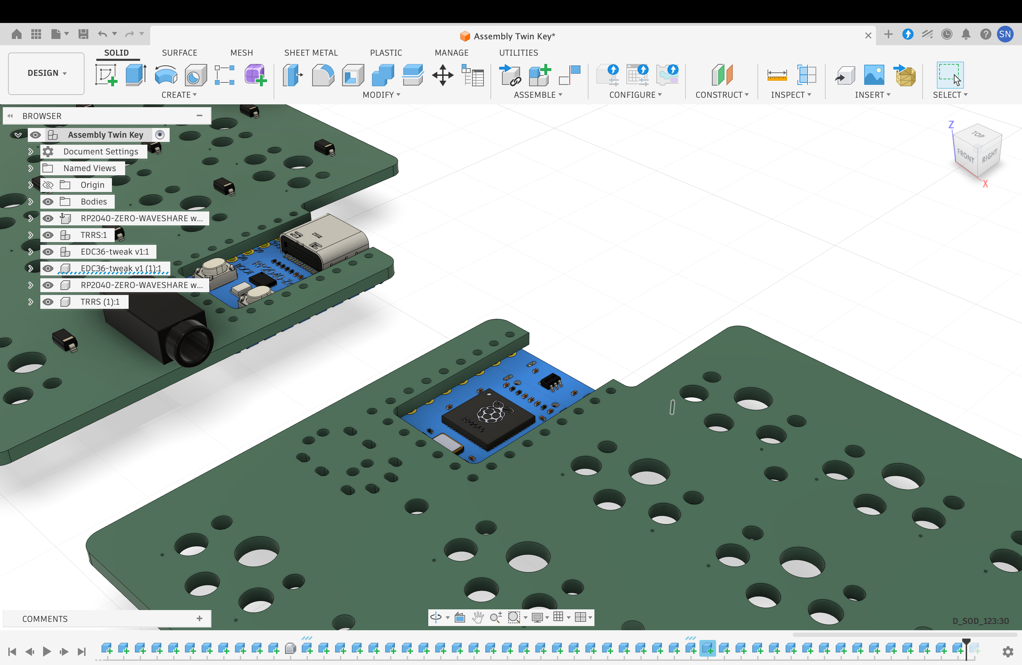
Images/30.png
