Sadrita404/Twin-Key/Images/31.png

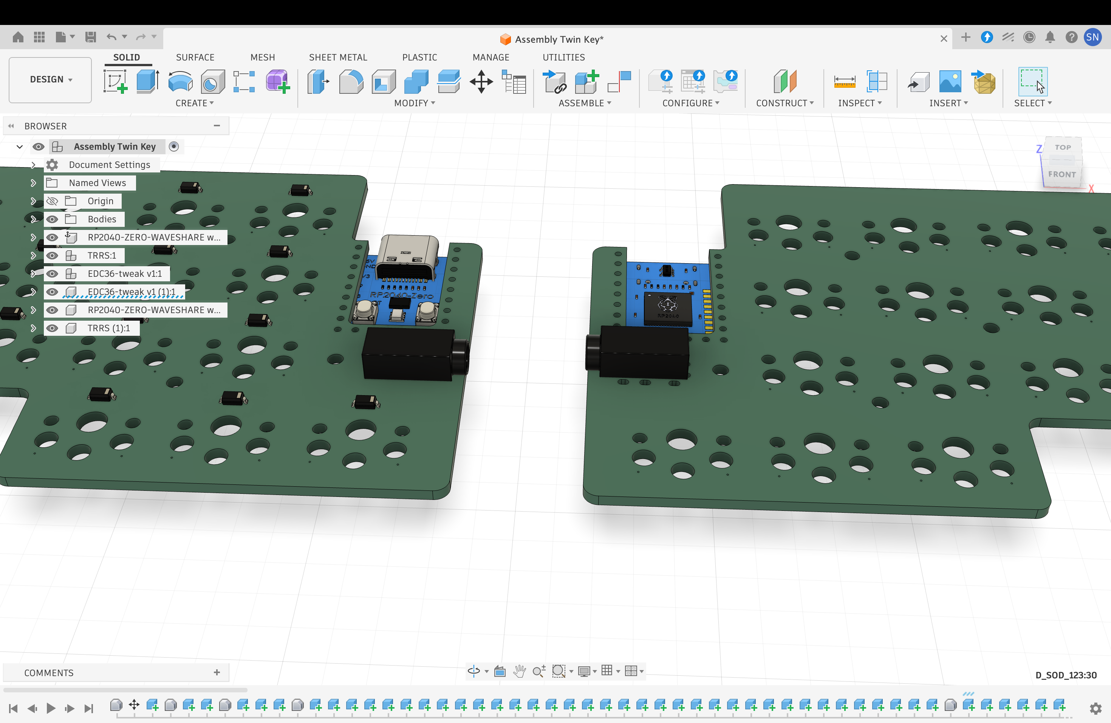
Images/31.png
