Sadrita404/Twin-Key/Images/32.png

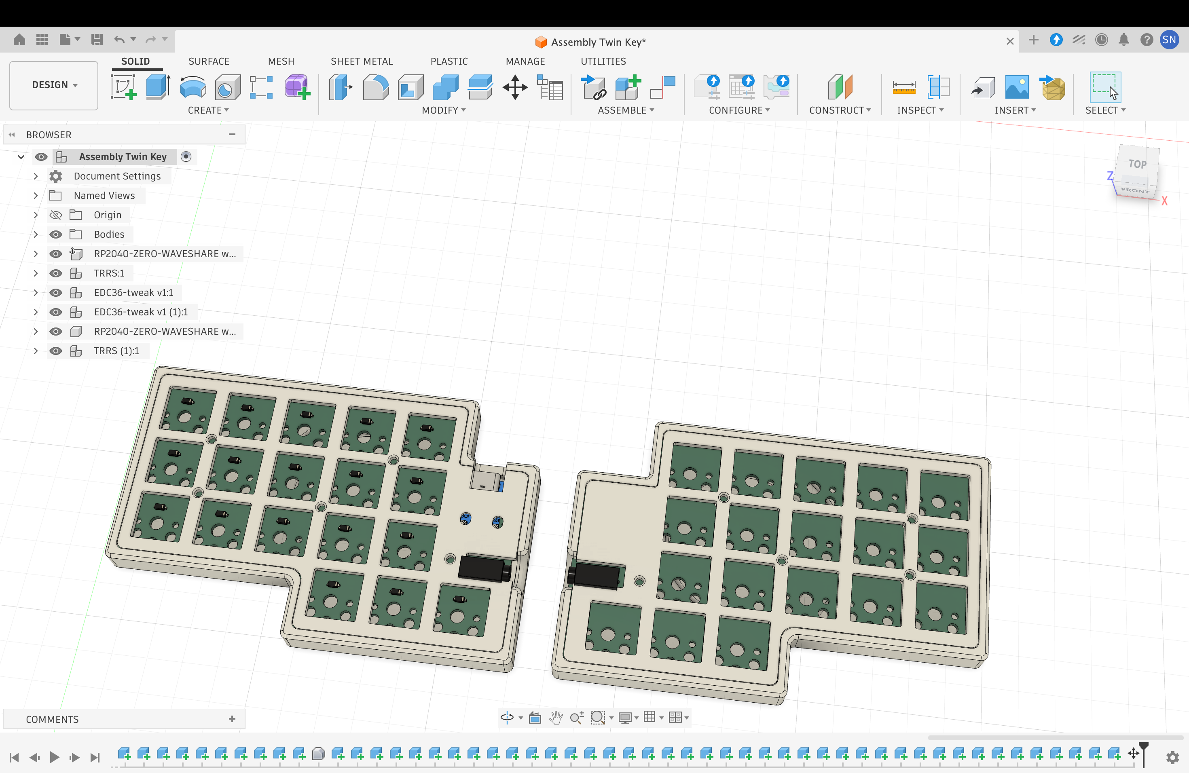
Images/32.png
