Sadrita404/Twin-Key/Images/33.png

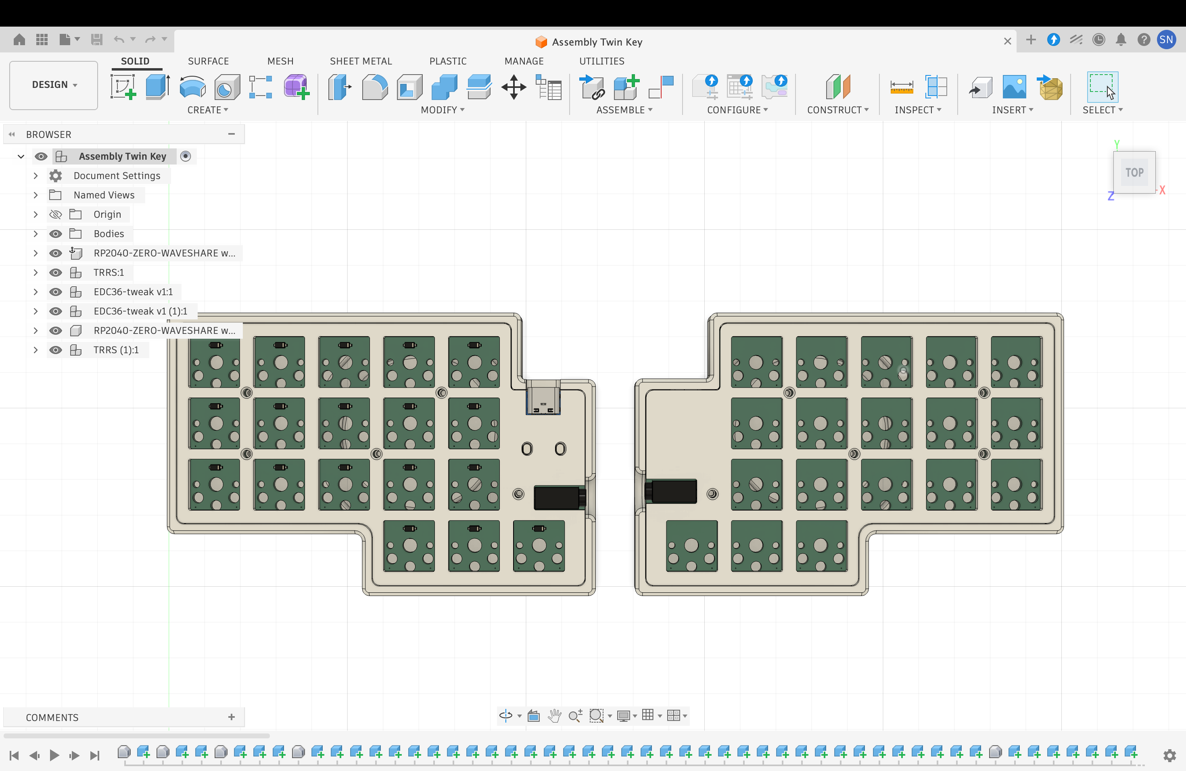
Images/33.png
