Sadrita404/Twin-Key/Images/34.png

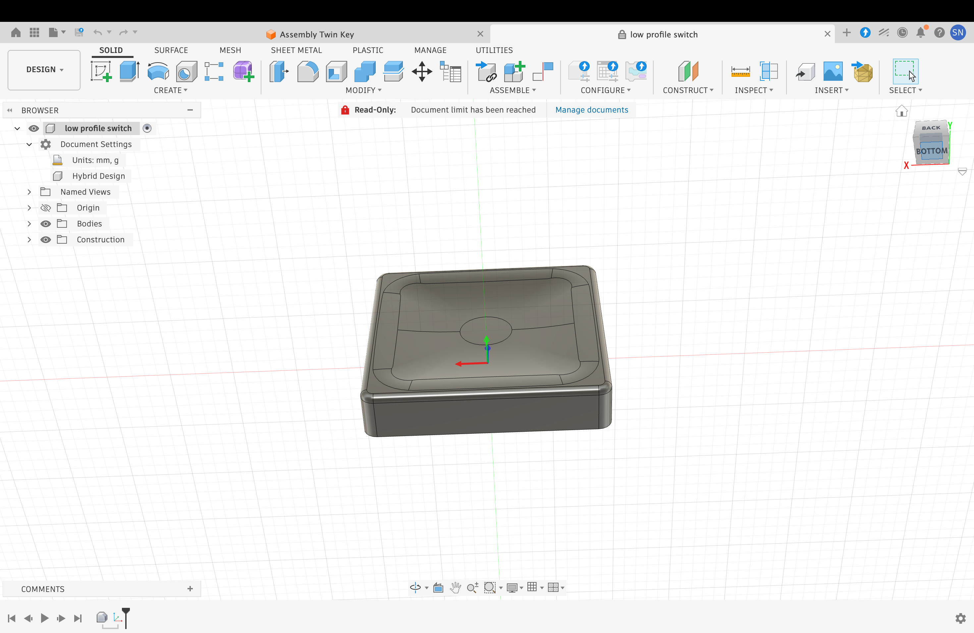
Images/34.png
