Sadrita404/Twin-Key/Images/35.png

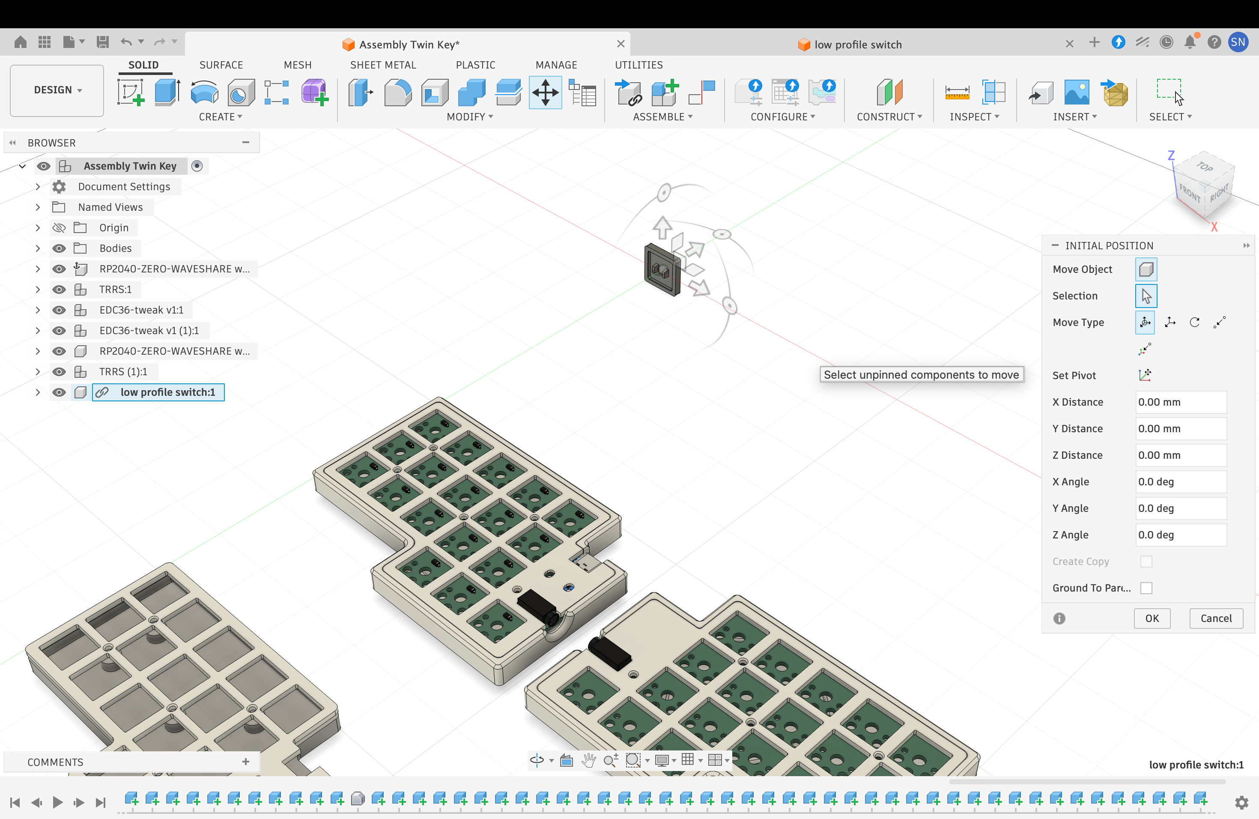
Images/35.png
