Sadrita404/Twin-Key/Images/36.png

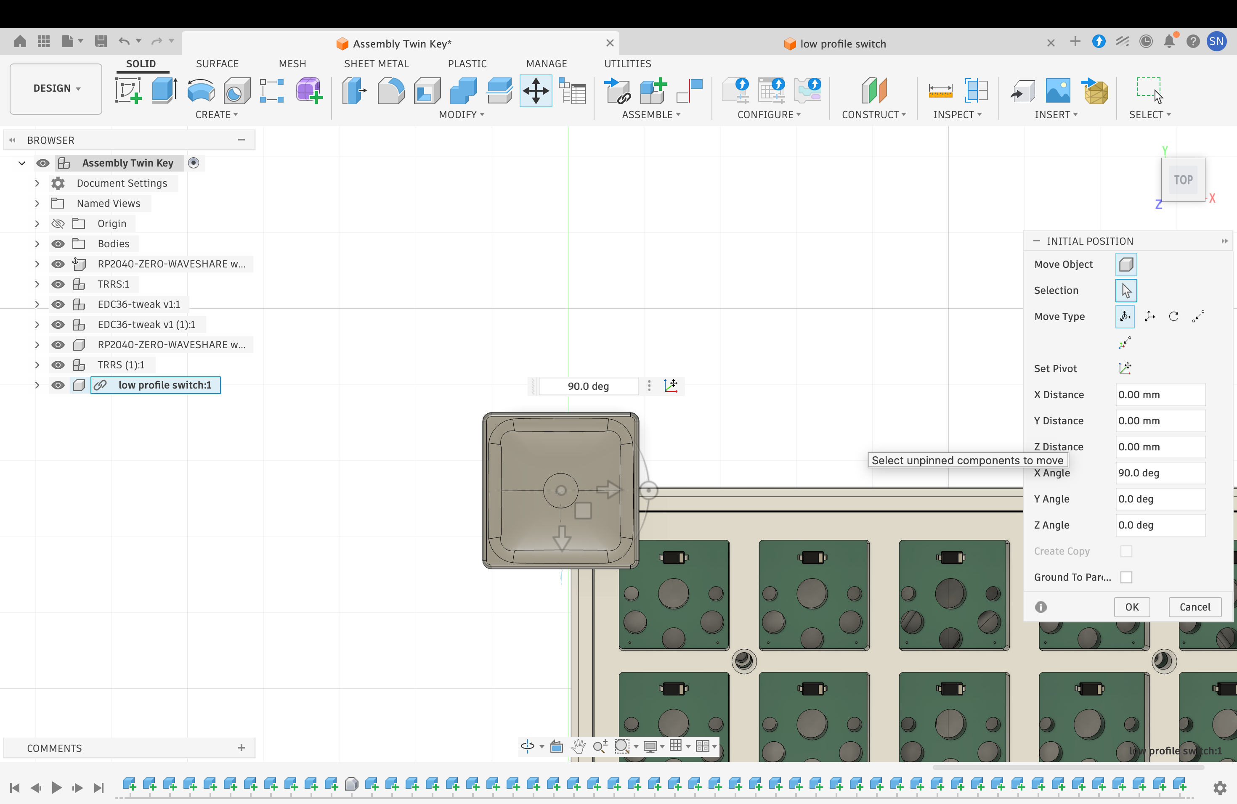
Images/36.png
