Sadrita404/Twin-Key/Images/37.png

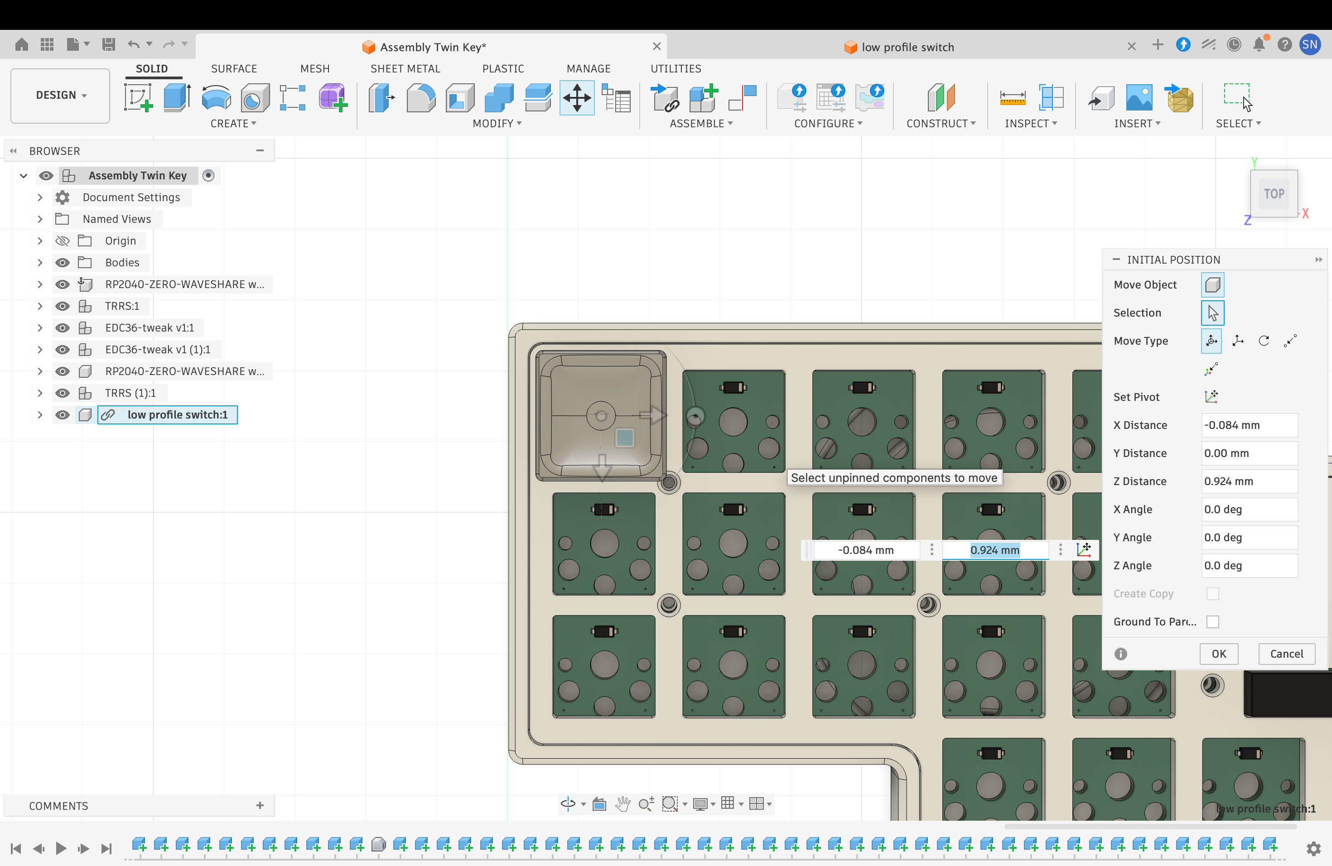
Images/37.png
