Sadrita404/Twin-Key/Images/38.png

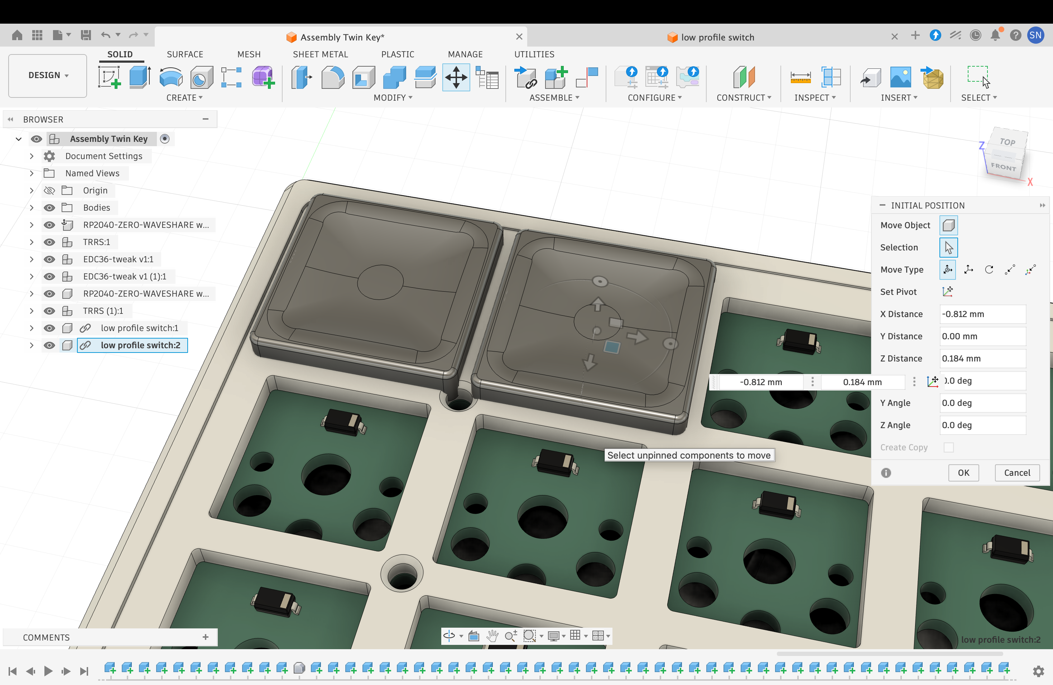
Images/38.png
