Sadrita404/Twin-Key/Images/39.png

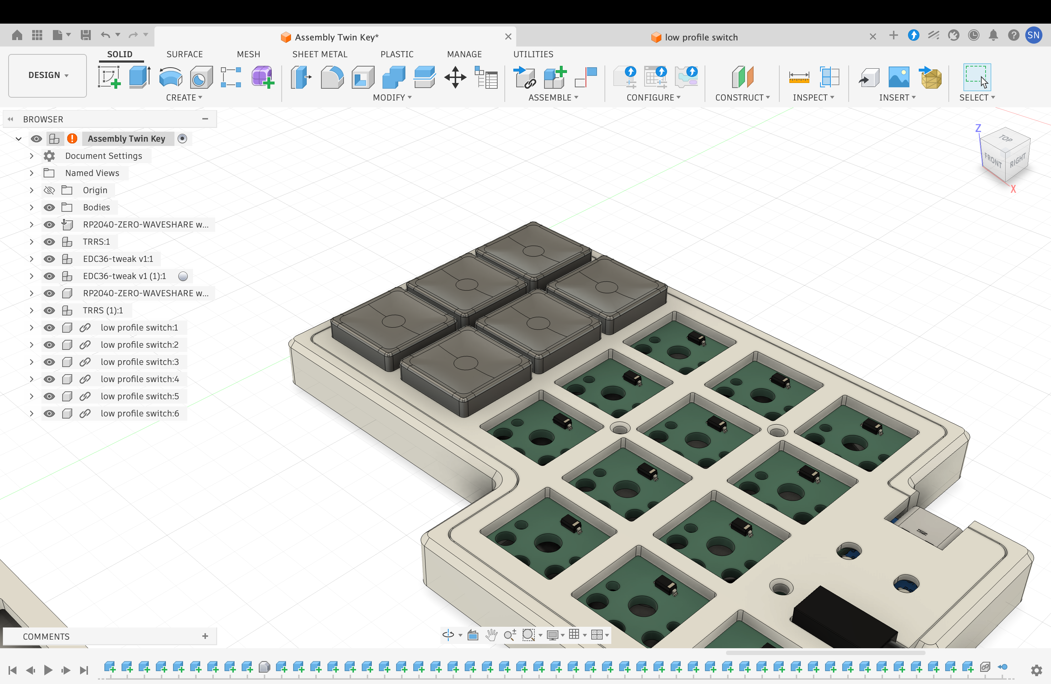
Images/39.png
