Sadrita404/Twin-Key/Images/40.png

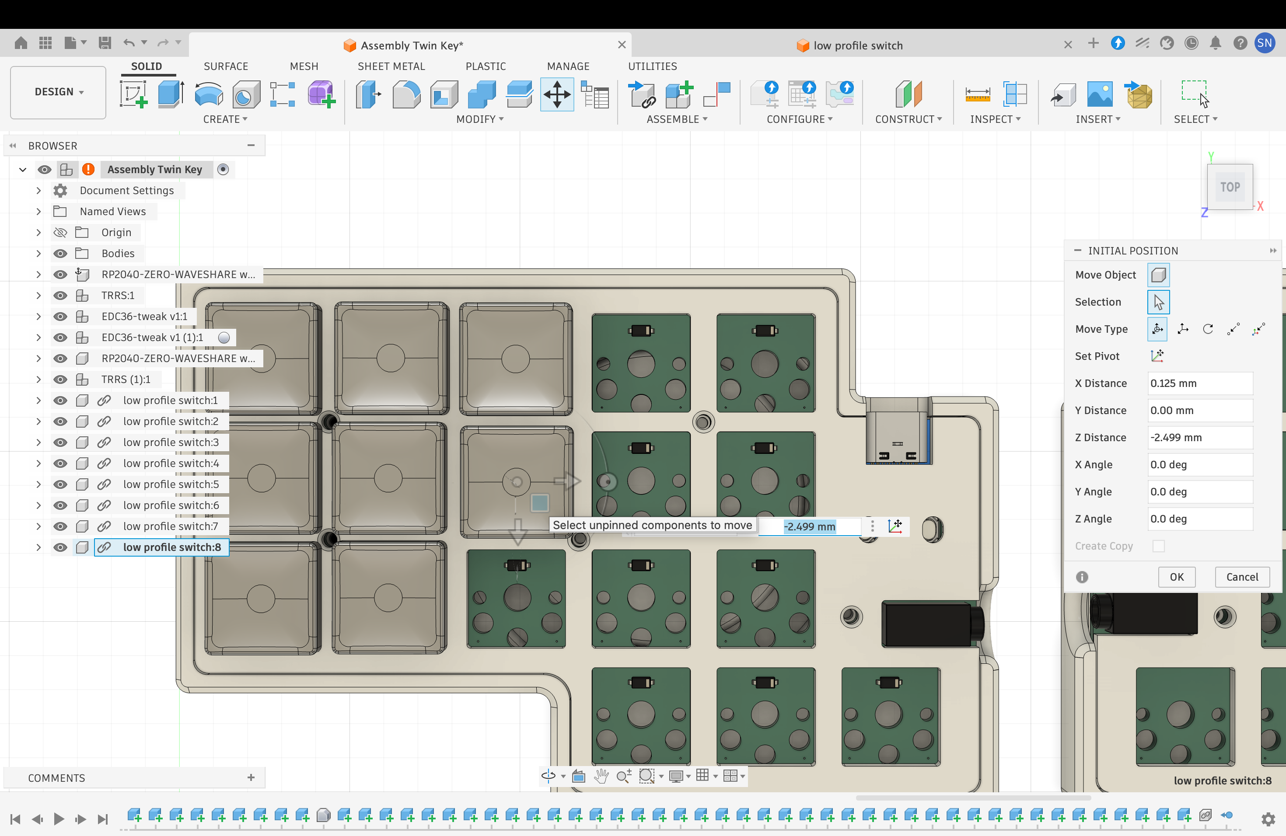
Images/40.png
