Sadrita404/Twin-Key/Images/41.png

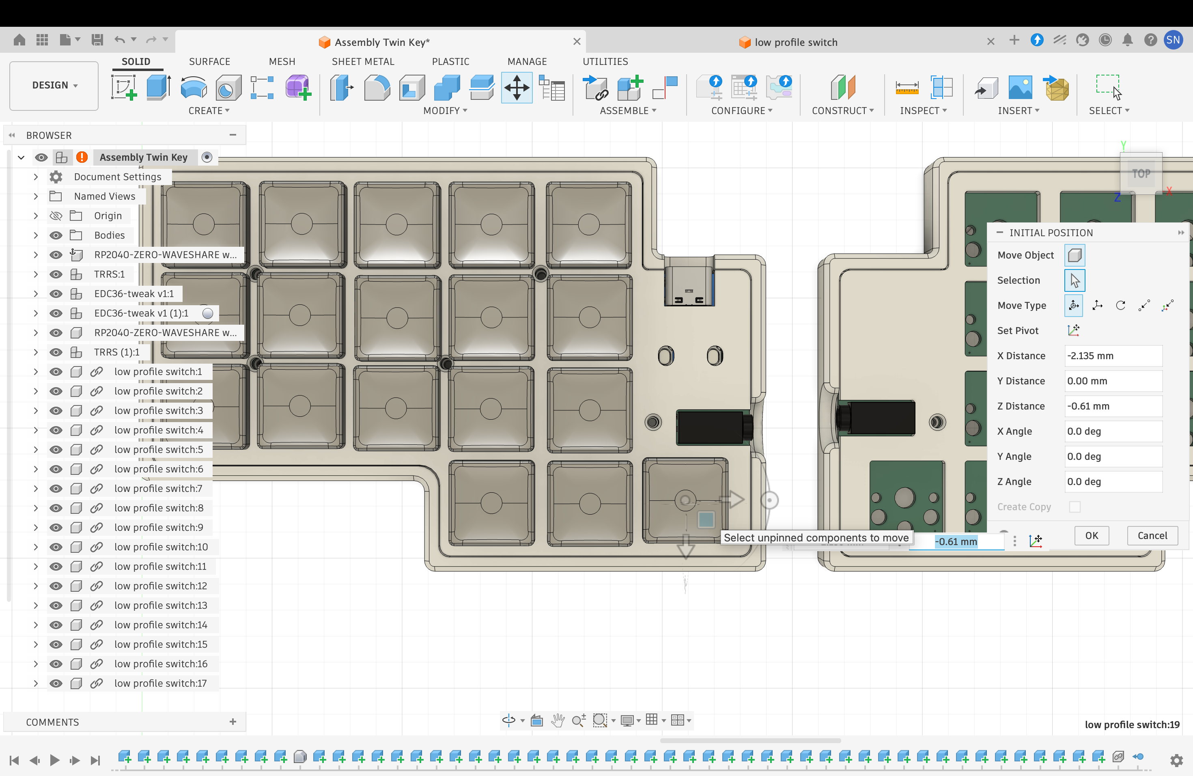
Images/41.png
