Sadrita404/Twin-Key/Images/42.png

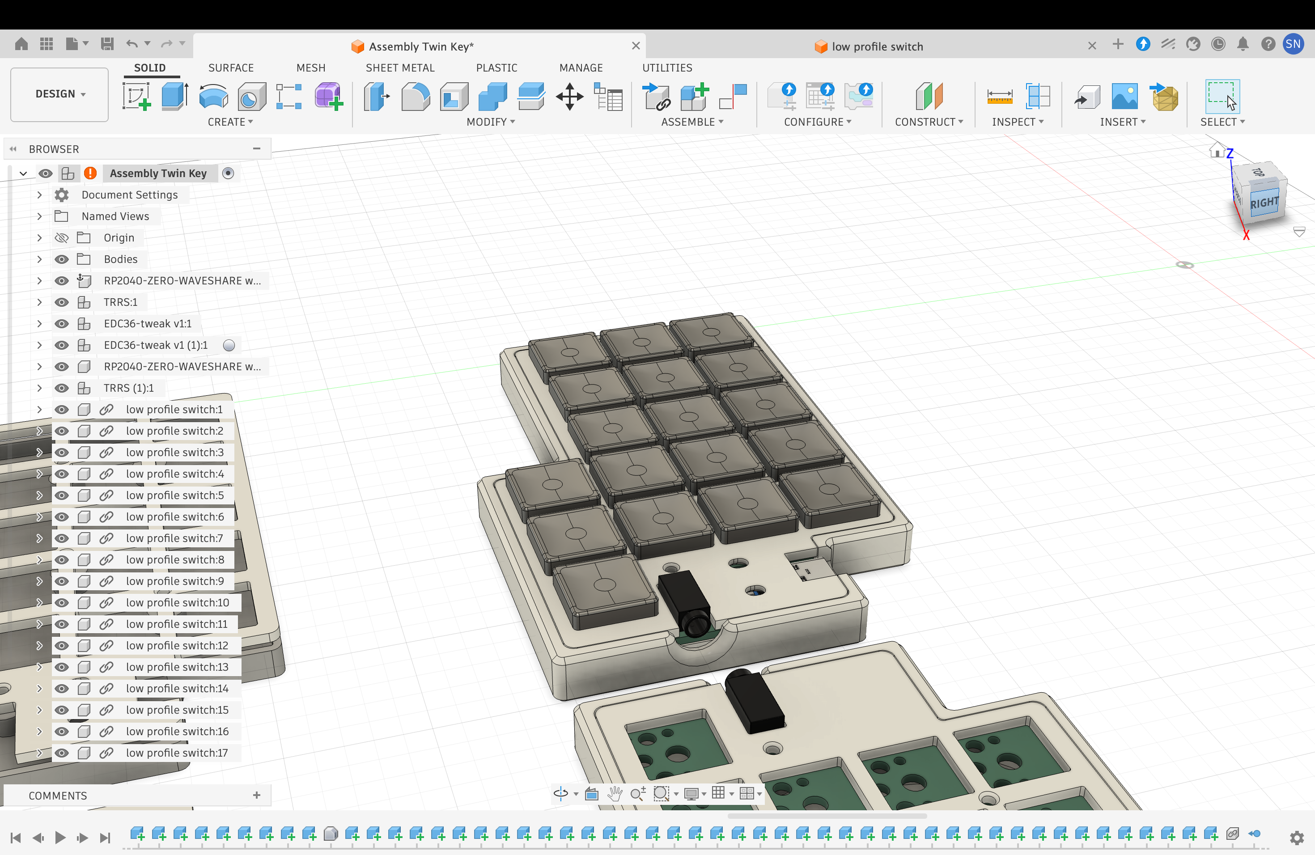
Images/42.png
