Sadrita404/Twin-Key/Images/43.png

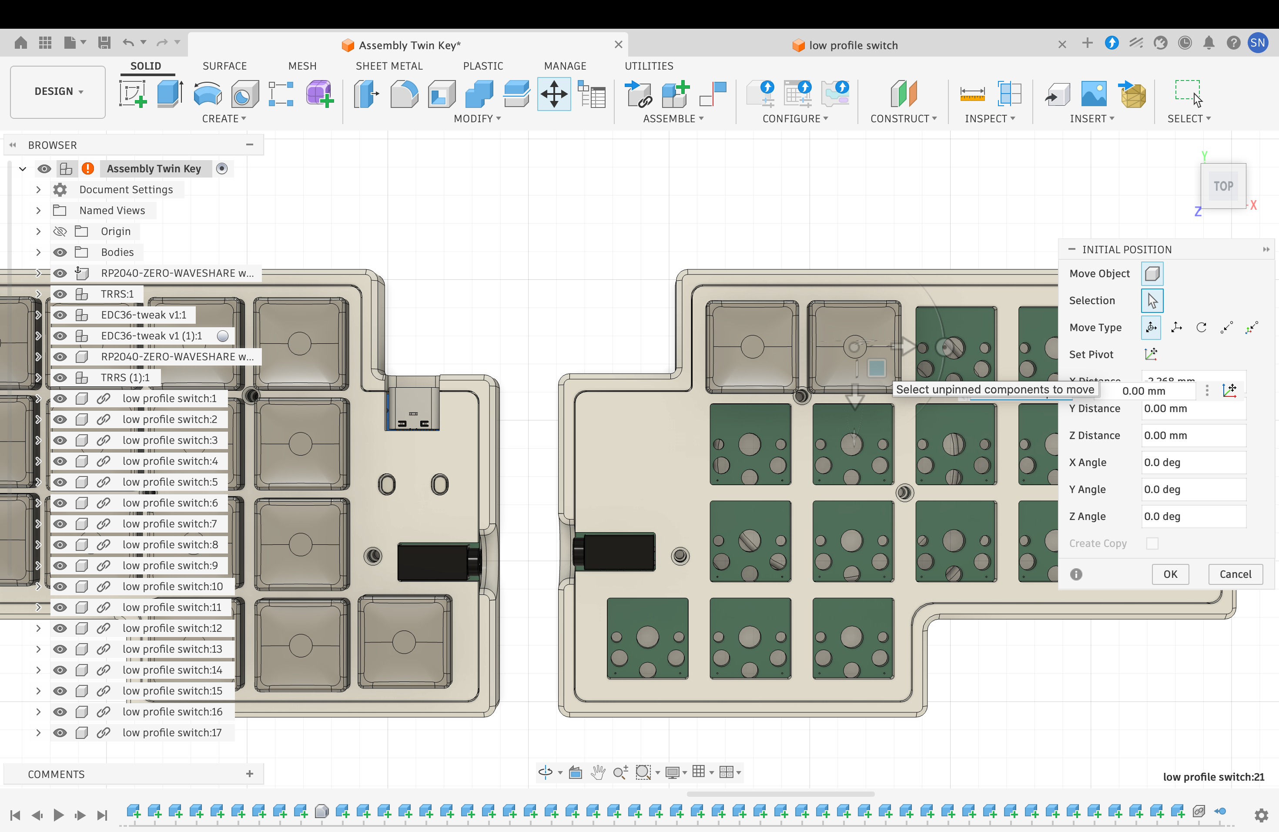
Images/43.png
