Sadrita404/Twin-Key/Images/44.png

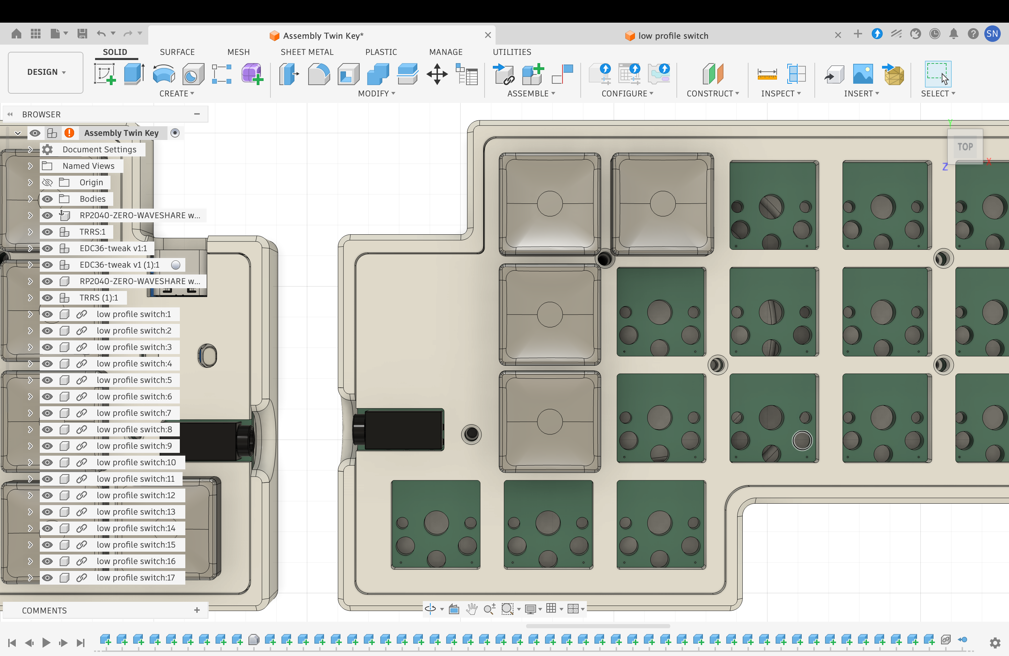
Images/44.png
