Sadrita404/Twin-Key/Images/45.png

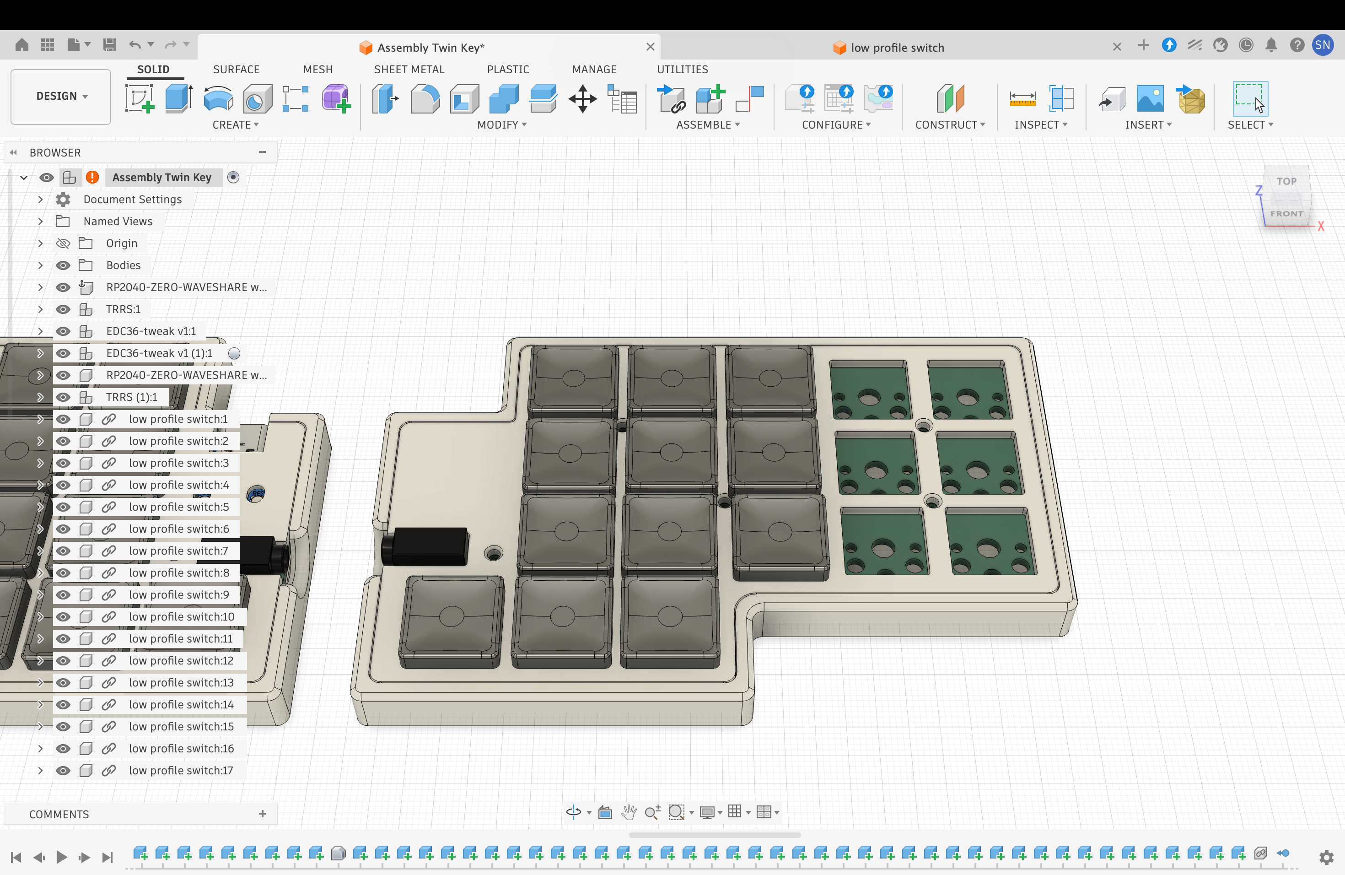
Images/45.png
