Sadrita404/Twin-Key/Images/46.png

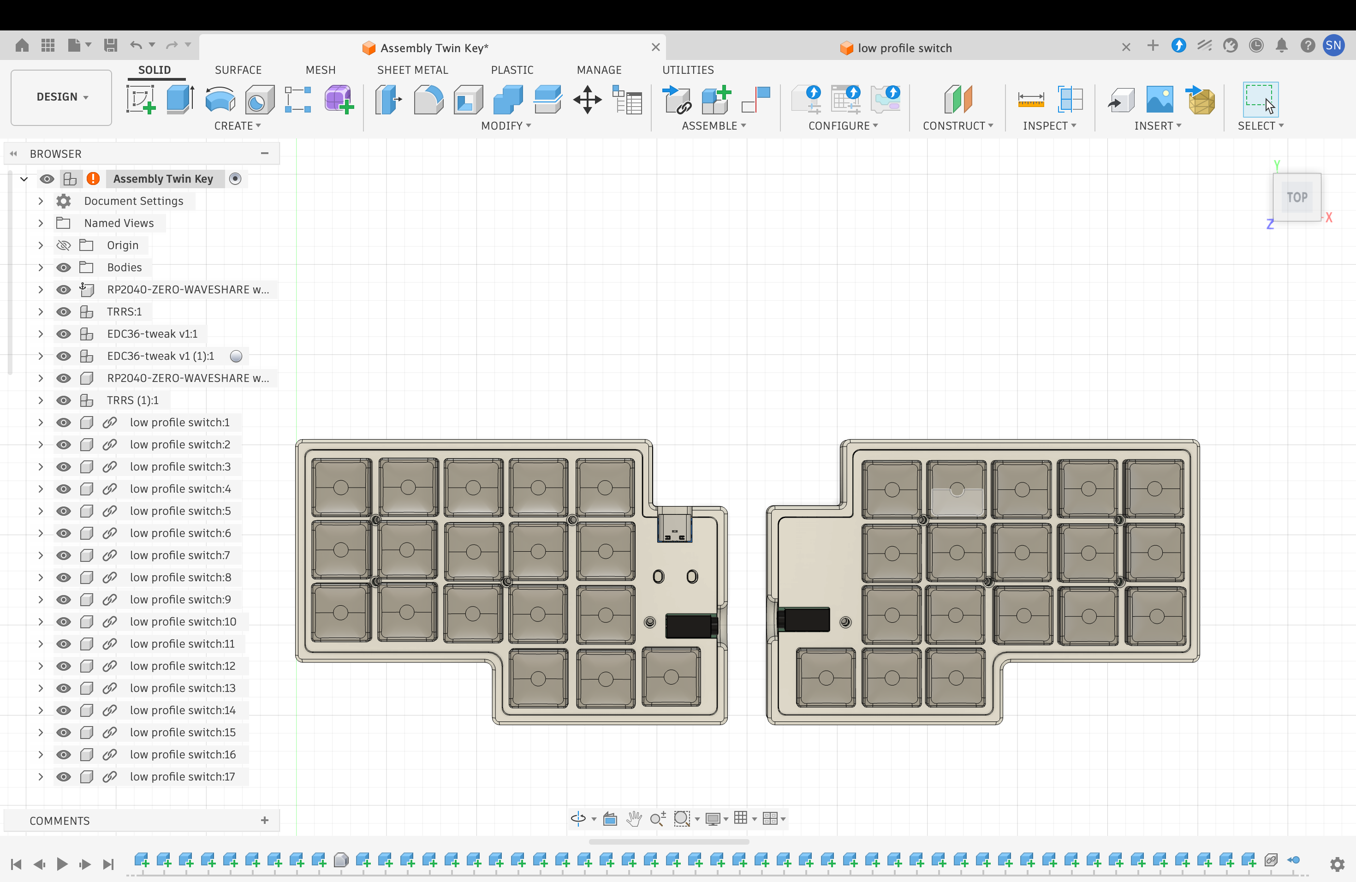
Images/46.png
