Sadrita404/Twin-Key/Images/47.png

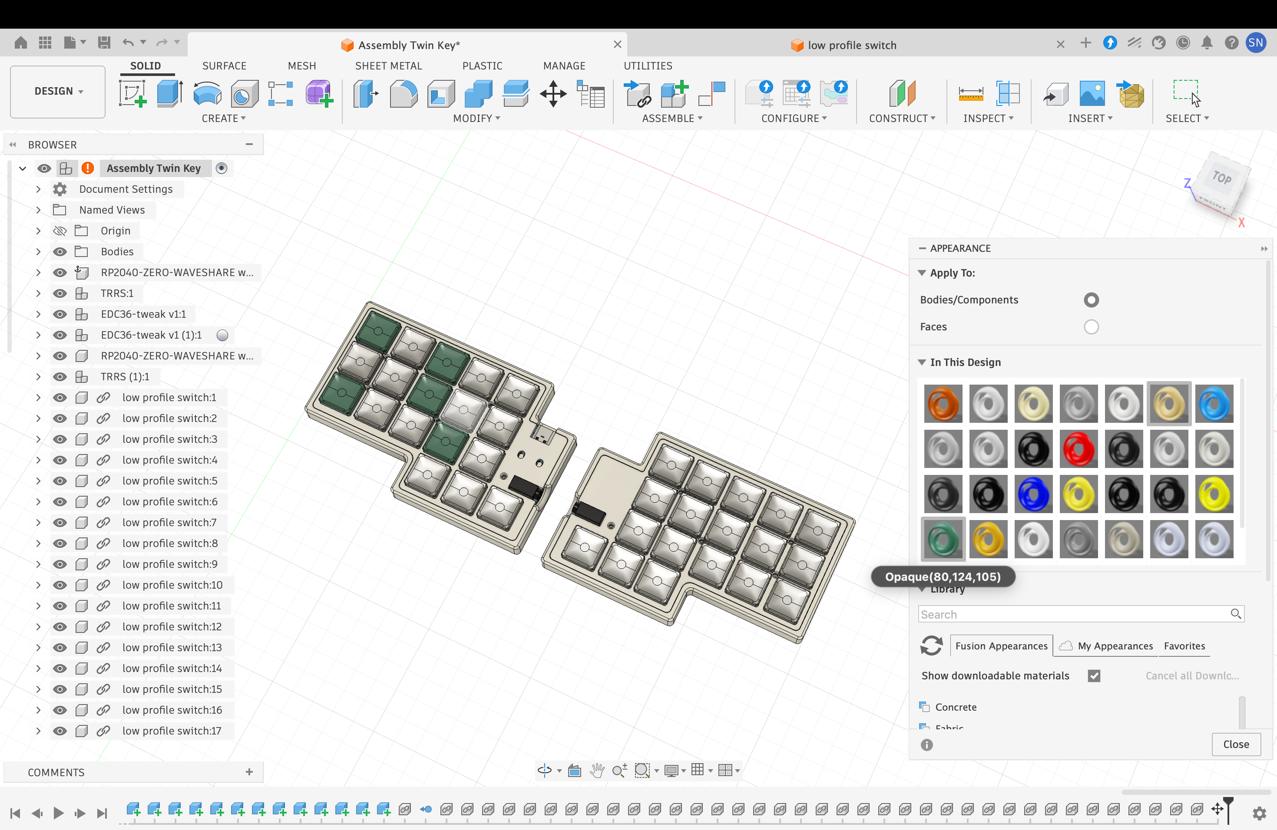
Images/47.png
