Sadrita404/Twin-Key/Images/49.png

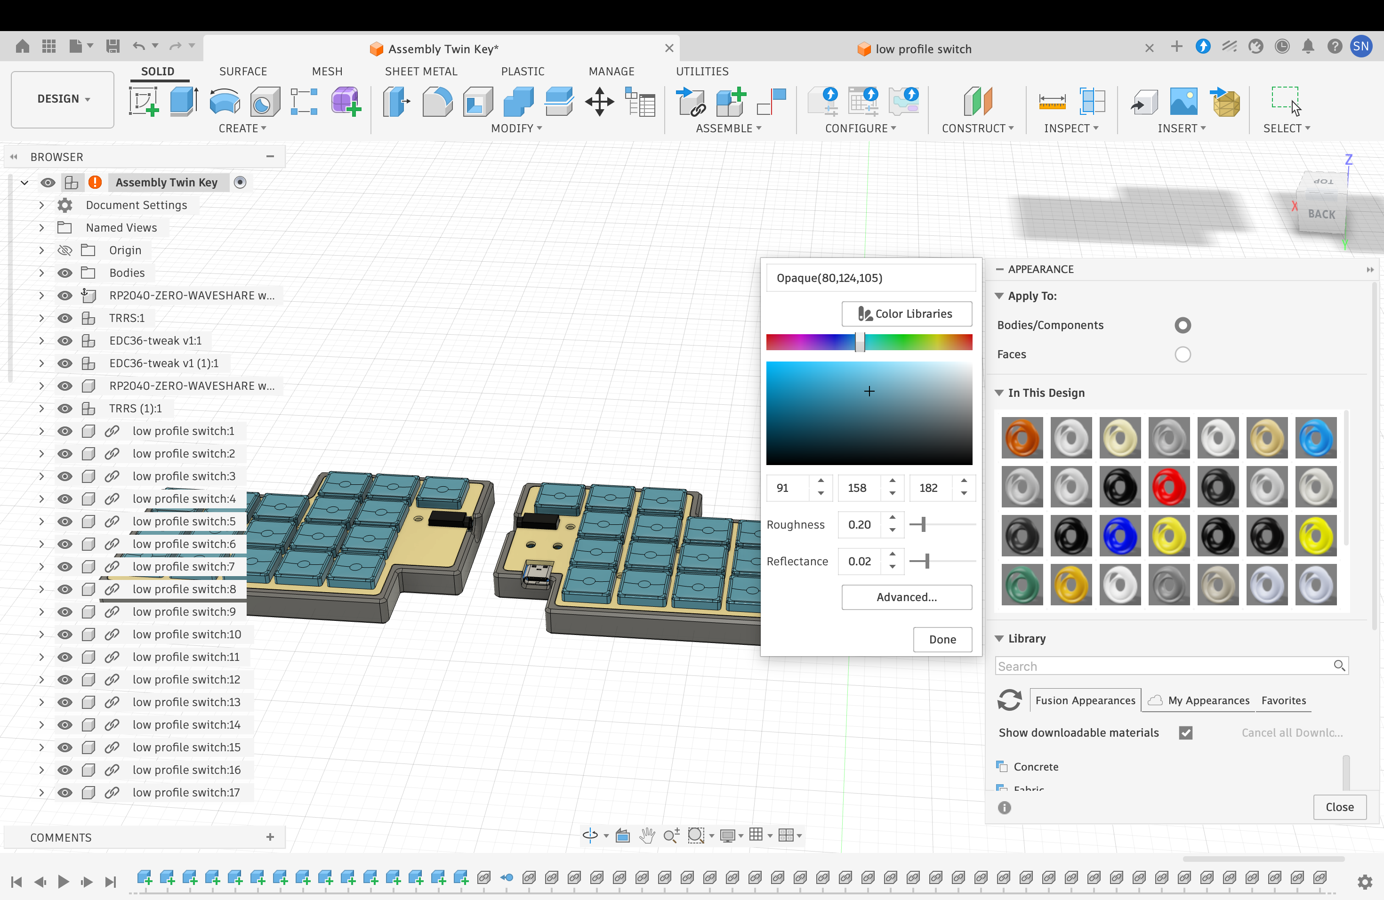
Images/49.png
