Sadrita404/Twin-Key/Images/50.png

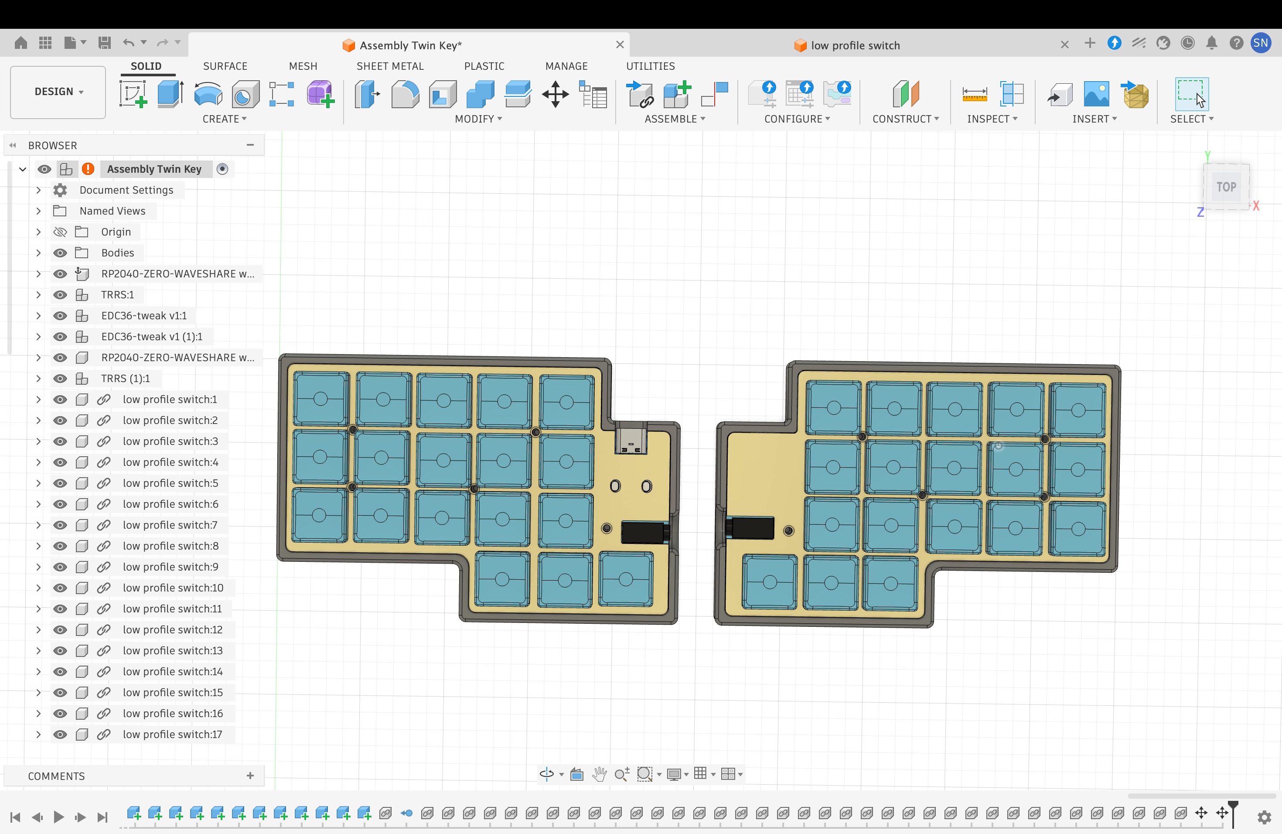
Images/50.png
