Sadrita404/Twin-Key/Images/51.png

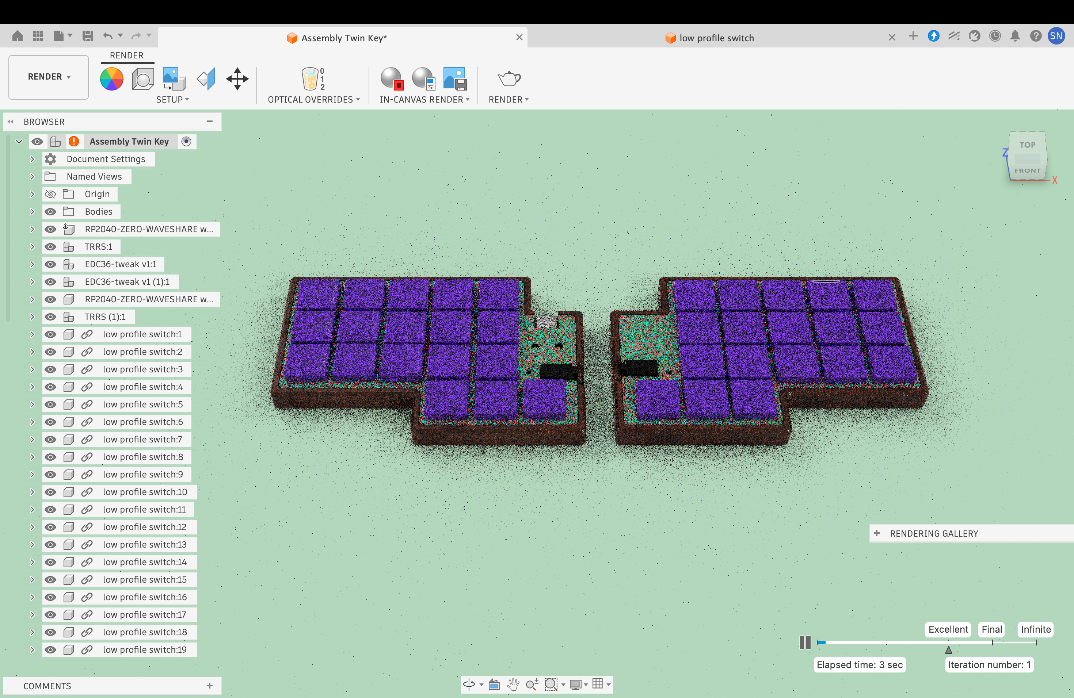
Images/51.png
