Sadrita404/Twin-Key/Images/52.jpg

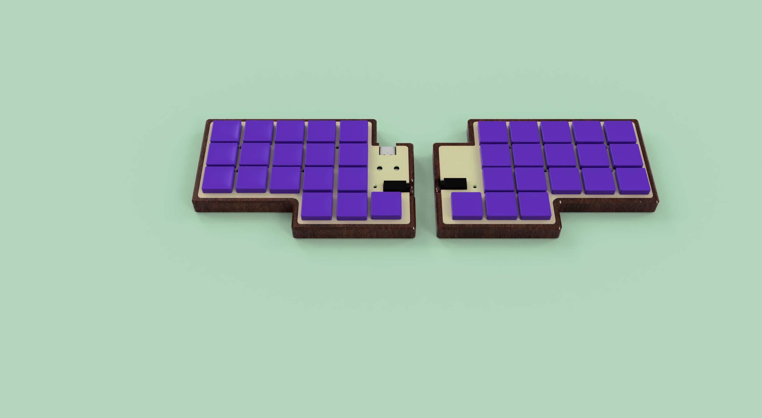
Images/52.jpg
